KomplexKapharnaum/KXKM_Batterie_Parallelator/docs/superpowers/plans/2026-04-08-i2c-hotplug.md

# I2C Hotplug — Differential Re-scan Implementation Plan

> **For agentic workers:** REQUIRED SUB-SKILL: Use superpowers:subagent-driven-development (recommended) or superpowers:executing-plans to implement this plan task-by-task. Steps use checkbox (`- [ ]`) syntax for tracking.

**Goal:** Enable runtime plug & play of I2C battery modules (INA237 + TCA9535) without reboot — differential re-scan every 10s detects added/removed devices and updates topology atomically.

**Architecture:** A new `bmu_i2c_hotplug` component provides a FreeRTOS task that periodically probes known I2C address ranges, compares with current topology, initializes new devices, marks removed devices, and updates `nb_ina`/`nb_tca` in protection + battery_manager + BLE + display contexts under mutex. All existing arrays are already sized to `BMU_MAX_BATTERIES=32` / `BMU_MAX_TCA=8`, so no dynamic allocation is needed.

**Tech Stack:** ESP-IDF 5.4, FreeRTOS, I2C master driver, existing `bmu_i2c` mutex

---

## File Structure

| Action | File | Responsibility |
|---|---|---|
| Create | `components/bmu_i2c_hotplug/bmu_i2c_hotplug.cpp` | Differential scan task + topology update logic |
| Create | `components/bmu_i2c_hotplug/include/bmu_i2c_hotplug.h` | Public API (init, start, stop, get stats) |
| Create | `components/bmu_i2c_hotplug/CMakeLists.txt` | Component registration |
| Create | `components/bmu_i2c_hotplug/Kconfig` | Config: enable, scan interval, log level |
| Modify | `main/main.cpp` | Wire hotplug task after boot scan, remove stale comment |
| Modify | `components/bmu_protection/include/bmu_protection.h` | Add `bmu_protection_update_topology()` |
| Modify | `components/bmu_protection/bmu_protection.cpp` | Implement topology update under mutex |
| Modify | `components/bmu_protection/include/bmu_battery_manager.h` | Add `bmu_battery_manager_update_nb_ina()` |

---

### Task 1: Create bmu_i2c_hotplug component scaffold

**Files:**
- Create: `components/bmu_i2c_hotplug/CMakeLists.txt`
- Create: `components/bmu_i2c_hotplug/Kconfig`
- Create: `components/bmu_i2c_hotplug/include/bmu_i2c_hotplug.h`
- Create: `components/bmu_i2c_hotplug/bmu_i2c_hotplug.cpp`

- [ ] **Step 1: Create CMakeLists.txt**

```cmake
idf_component_register(
    SRCS "bmu_i2c_hotplug.cpp"
    INCLUDE_DIRS "include"
    REQUIRES bmu_i2c bmu_ina237 bmu_tca9535 bmu_protection bmu_config
    PRIV_REQUIRES esp_timer
)
```

- [ ] **Step 2: Create Kconfig**

```kconfig
menu "BMU I2C Hotplug"

    config BMU_I2C_HOTPLUG_ENABLED
        bool "Enable I2C hotplug (periodic re-scan)"
        default y
        help
            Periodically re-scans the I2C bus to detect added/removed
            INA237 and TCA9535 devices at runtime.

    config BMU_I2C_HOTPLUG_INTERVAL_S
        int "Re-scan interval (seconds)"
        default 10
        range 5 60
        depends on BMU_I2C_HOTPLUG_ENABLED

    config BMU_I2C_HOTPLUG_STACK_SIZE
        int "Task stack size (bytes)"
        default 3072
        depends on BMU_I2C_HOTPLUG_ENABLED

    config BMU_I2C_HOTPLUG_TASK_PRIORITY
        int "Task priority"
        default 3
        depends on BMU_I2C_HOTPLUG_ENABLED

endmenu
```

- [ ] **Step 3: Create header bmu_i2c_hotplug.h**

```cpp
#pragma once

#include "bmu_ina237.h"
#include "bmu_tca9535.h"
#include "bmu_protection.h"
#include "bmu_battery_manager.h"
#include "esp_err.h"

#ifdef __cplusplus
extern "C" {
#endif

typedef struct {
    i2c_master_bus_handle_t  bus;
    bmu_ina237_t            *ina_devices;    /* static array [BMU_MAX_BATTERIES] */
    bmu_tca9535_handle_t    *tca_devices;    /* static array [BMU_MAX_TCA] */
    uint8_t                 *nb_ina;         /* pointer to live counter */
    uint8_t                 *nb_tca;         /* pointer to live counter */
    bool                    *topology_ok;    /* pointer to live flag */
    bmu_protection_ctx_t    *prot;
    bmu_battery_manager_t   *mgr;
} bmu_hotplug_cfg_t;

typedef struct {
    uint32_t scan_count;       /* total scans performed */
    uint32_t topo_changes;     /* topology changes detected */
    uint8_t  last_nb_ina;      /* nb_ina after last scan */
    uint8_t  last_nb_tca;      /* nb_tca after last scan */
} bmu_hotplug_stats_t;

/**
 * @brief Initialize hotplug task (does not start scanning).
 */
esp_err_t bmu_hotplug_init(const bmu_hotplug_cfg_t *cfg);

/**
 * @brief Start periodic scanning task.
 */
esp_err_t bmu_hotplug_start(void);

/**
 * @brief Stop periodic scanning task.
 */
esp_err_t bmu_hotplug_stop(void);

/**
 * @brief Get scan statistics.
 */
void bmu_hotplug_get_stats(bmu_hotplug_stats_t *stats);

#ifdef __cplusplus
}
#endif
```

- [ ] **Step 4: Create stub implementation bmu_i2c_hotplug.cpp**

```cpp
#include "bmu_i2c_hotplug.h"
#include "bmu_i2c.h"
#include "bmu_config.h"
#include "esp_log.h"
#include "freertos/FreeRTOS.h"
#include "freertos/task.h"

static const char *TAG = "HOTPLUG";

static bmu_hotplug_cfg_t   s_cfg = {};
static bmu_hotplug_stats_t s_stats = {};
static TaskHandle_t        s_task = NULL;
static bool                s_initialized = false;

esp_err_t bmu_hotplug_init(const bmu_hotplug_cfg_t *cfg)
{
    if (cfg == NULL || cfg->bus == NULL) return ESP_ERR_INVALID_ARG;
    s_cfg = *cfg;
    s_initialized = true;
    ESP_LOGI(TAG, "Hotplug initialized — interval %ds", CONFIG_BMU_I2C_HOTPLUG_INTERVAL_S);
    return ESP_OK;
}

static void hotplug_task(void *pv);

esp_err_t bmu_hotplug_start(void)
{
    if (!s_initialized) return ESP_ERR_INVALID_STATE;
    if (s_task != NULL) return ESP_ERR_INVALID_STATE;

    BaseType_t ret = xTaskCreate(hotplug_task, "hotplug",
                                 CONFIG_BMU_I2C_HOTPLUG_STACK_SIZE,
                                 NULL, CONFIG_BMU_I2C_HOTPLUG_TASK_PRIORITY,
                                 &s_task);
    return (ret == pdPASS) ? ESP_OK : ESP_ERR_NO_MEM;
}

esp_err_t bmu_hotplug_stop(void)
{
    if (s_task != NULL) {
        vTaskDelete(s_task);
        s_task = NULL;
    }
    return ESP_OK;
}

void bmu_hotplug_get_stats(bmu_hotplug_stats_t *stats)
{
    if (stats) *stats = s_stats;
}

/* Placeholder — implemented in Task 3 */
static void hotplug_task(void *pv)
{
    const TickType_t period = pdMS_TO_TICKS(CONFIG_BMU_I2C_HOTPLUG_INTERVAL_S * 1000);
    for (;;) {
        vTaskDelay(period);
        s_stats.scan_count++;
        ESP_LOGD(TAG, "Scan #%lu (stub)", (unsigned long)s_stats.scan_count);
    }
}
```

- [ ] **Step 5: Build to verify component compiles**

Run: `source ~/esp/esp-idf/export.sh && cd firmware-idf && idf.py build 2>&1 | tail -5`
Expected: Build success (component auto-discovered by ESP-IDF)

- [ ] **Step 6: Commit**

```bash
git add firmware-idf/components/bmu_i2c_hotplug/
git commit -m "feat(hotplug): scaffold bmu_i2c_hotplug component with Kconfig + stub task"
```

---

### Task 2: Add topology update API to protection + battery_manager

**Files:**
- Modify: `components/bmu_protection/include/bmu_protection.h`
- Modify: `components/bmu_protection/bmu_protection.cpp`
- Modify: `components/bmu_protection/include/bmu_battery_manager.h`

- [ ] **Step 1: Add bmu_protection_update_topology declaration**

In `components/bmu_protection/include/bmu_protection.h`, add before the closing `#ifdef __cplusplus`:

```c
/**
 * @brief Update topology counts after hotplug re-scan.
 * Resets state of new battery slots to DISCONNECTED.
 * Must be called with valid nb_ina <= BMU_MAX_BATTERIES and nb_tca <= BMU_MAX_TCA.
 */
esp_err_t bmu_protection_update_topology(bmu_protection_ctx_t *ctx,
                                          uint8_t new_nb_ina,
                                          uint8_t new_nb_tca);
```

- [ ] **Step 2: Implement bmu_protection_update_topology**

In `components/bmu_protection/bmu_protection.cpp`, add before the closing brace:

```cpp
esp_err_t bmu_protection_update_topology(bmu_protection_ctx_t *ctx,
                                          uint8_t new_nb_ina,
                                          uint8_t new_nb_tca)
{
    if (new_nb_ina > BMU_MAX_BATTERIES || new_nb_tca > BMU_MAX_TCA) {
        return ESP_ERR_INVALID_ARG;
    }

    if (xSemaphoreTake(ctx->state_mutex, pdMS_TO_TICKS(100)) != pdTRUE) {
        return ESP_ERR_TIMEOUT;
    }

    uint8_t old_nb_ina = ctx->nb_ina;

    /* Init state for newly added battery slots */
    for (int i = old_nb_ina; i < new_nb_ina; i++) {
        ctx->battery_state[i] = BMU_STATE_DISCONNECTED;
        ctx->battery_voltages[i] = 0;
        ctx->nb_switch[i] = 0;
        ctx->reconnect_time_ms[i] = 0;
    }

    /* Clear state for removed battery slots */
    for (int i = new_nb_ina; i < old_nb_ina; i++) {
        ctx->battery_state[i] = BMU_STATE_DISCONNECTED;
        ctx->battery_voltages[i] = 0;
        ctx->nb_switch[i] = 0;
        ctx->reconnect_time_ms[i] = 0;
    }

    ctx->nb_ina = new_nb_ina;
    ctx->nb_tca = new_nb_tca;

    xSemaphoreGive(ctx->state_mutex);

    if (new_nb_ina != old_nb_ina) {
        ESP_LOGI(TAG, "Topology updated: %d→%d INA, %d TCA",
                 old_nb_ina, new_nb_ina, new_nb_tca);
    }

    return ESP_OK;
}
```

- [ ] **Step 3: Add bmu_battery_manager_update_nb_ina declaration**

In `components/bmu_protection/include/bmu_battery_manager.h`, add before closing `#ifdef __cplusplus`:

```c
/**
 * @brief Update nb_ina after hotplug topology change.
 */
esp_err_t bmu_battery_manager_update_nb_ina(bmu_battery_manager_t *mgr, uint8_t new_nb_ina);
```

- [ ] **Step 4: Implement bmu_battery_manager_update_nb_ina**

Find `bmu_battery_manager.cpp` and add:

```cpp
esp_err_t bmu_battery_manager_update_nb_ina(bmu_battery_manager_t *mgr, uint8_t new_nb_ina)
{
    if (new_nb_ina > BMU_MAX_BATTERIES) return ESP_ERR_INVALID_ARG;

    if (xSemaphoreTake(mgr->mutex, pdMS_TO_TICKS(100)) != pdTRUE) {
        return ESP_ERR_TIMEOUT;
    }

    uint8_t old = mgr->nb_ina;

    /* Reset Ah counters for new slots */
    for (int i = old; i < new_nb_ina; i++) {
        mgr->last_voltage_mv[i] = 0;
        mgr->last_current_a[i] = 0;
        mgr->ah_discharge[i] = 0;
        mgr->ah_charge[i] = 0;
    }

    mgr->nb_ina = new_nb_ina;
    xSemaphoreGive(mgr->mutex);

    return ESP_OK;
}
```

- [ ] **Step 5: Build**

Run: `cd firmware-idf && idf.py build 2>&1 | tail -5`
Expected: Build success

- [ ] **Step 6: Commit**

```bash
git add firmware-idf/components/bmu_protection/
git commit -m "feat(protection): add bmu_protection_update_topology + battery_manager update for hotplug"
```

---

### Task 3: Implement differential scan logic

**Files:**
- Modify: `components/bmu_i2c_hotplug/bmu_i2c_hotplug.cpp`

- [ ] **Step 1: Replace the stub hotplug_task with differential scan**

Replace the entire `hotplug_task` function in `bmu_i2c_hotplug.cpp`:

```cpp
/* ── Differential scan: probe existing + discover new ────────────── */

/**
 * @brief Quick health-check: probe an existing device address.
 * @return true if device still responds
 */
static bool device_still_present(uint8_t addr)
{
    return bmu_i2c_probe(s_cfg.bus, addr, pdMS_TO_TICKS(20)) == ESP_OK;
}

/**
 * @brief Scan for new INA237 devices not in the current array.
 * Returns count of newly initialized devices.
 */
static int scan_new_ina(void)
{
    int added = 0;
    uint8_t cur = *s_cfg.nb_ina;

    for (uint8_t addr = INA237_ADDR_MIN; addr <= INA237_ADDR_MAX && cur < BMU_MAX_BATTERIES; addr++) {
        /* Skip addresses already known */
        bool known = false;
        for (int i = 0; i < cur; i++) {
            if (s_cfg.ina_devices[i].addr == addr) { known = true; break; }
        }
        if (known) continue;

        /* Probe new address */
        if (bmu_i2c_probe(s_cfg.bus, addr, pdMS_TO_TICKS(20)) != ESP_OK) continue;

        /* Initialize new INA237 */
        esp_err_t ret = bmu_ina237_init(s_cfg.bus, addr,
                                         INA237_SHUNT_RESISTANCE_UOHM, 10.0f,
                                         &s_cfg.ina_devices[cur]);
        if (ret == ESP_OK) {
            ESP_LOGI(TAG, "NEW INA237 @ 0x%02X → slot %d", addr, cur);
            cur++;
            added++;
        } else {
            ESP_LOGW(TAG, "INA237 @ 0x%02X probe OK but init failed: %s",
                     addr, esp_err_to_name(ret));
        }
    }
    return added;
}

/**
 * @brief Scan for new TCA9535 devices not in the current array.
 * Returns count of newly initialized devices.
 */
static int scan_new_tca(void)
{
    int added = 0;
    uint8_t cur = *s_cfg.nb_tca;

    for (uint8_t addr = TCA9535_BASE_ADDR; addr < TCA9535_BASE_ADDR + TCA9535_MAX_DEVICES && cur < BMU_MAX_TCA; addr++) {
        bool known = false;
        for (int i = 0; i < cur; i++) {
            if (s_cfg.tca_devices[i].addr == addr) { known = true; break; }
        }
        if (known) continue;

        if (bmu_i2c_probe(s_cfg.bus, addr, pdMS_TO_TICKS(20)) != ESP_OK) continue;

        esp_err_t ret = bmu_tca9535_init(s_cfg.bus, addr, &s_cfg.tca_devices[cur]);
        if (ret == ESP_OK) {
            ESP_LOGI(TAG, "NEW TCA9535 @ 0x%02X → slot %d", addr, cur);
            cur++;
            added++;
        } else {
            ESP_LOGW(TAG, "TCA9535 @ 0x%02X probe OK but init failed: %s",
                     addr, esp_err_to_name(ret));
        }
    }
    return added;
}

/**
 * @brief Check existing devices for removal.
 * Returns count of removed INA237 devices.
 * Compacts array to fill gaps (maintains contiguous indexing).
 */
static int check_ina_removals(void)
{
    int removed = 0;
    uint8_t cur = *s_cfg.nb_ina;

    for (int i = 0; i < cur; ) {
        if (device_still_present(s_cfg.ina_devices[i].addr)) {
            bmu_i2c_record_success();
            i++;
        } else {
            ESP_LOGW(TAG, "INA237 @ 0x%02X GONE — removing slot %d",
                     s_cfg.ina_devices[i].addr, i);
            /* Remove I2C device handle */
            if (s_cfg.ina_devices[i].dev) {
                i2c_master_bus_rm_device(s_cfg.ina_devices[i].dev);
            }
            /* Compact: shift remaining entries left */
            for (int j = i; j < cur - 1; j++) {
                s_cfg.ina_devices[j] = s_cfg.ina_devices[j + 1];
            }
            memset(&s_cfg.ina_devices[cur - 1], 0, sizeof(bmu_ina237_t));
            cur--;
            removed++;
            /* Don't increment i — re-check the slot that shifted in */
        }
    }

    *s_cfg.nb_ina = cur;
    return removed;
}

/**
 * @brief Check existing TCA9535 devices for removal.
 * Compacts array. Returns count of removed devices.
 */
static int check_tca_removals(void)
{
    int removed = 0;
    uint8_t cur = *s_cfg.nb_tca;

    for (int i = 0; i < cur; ) {
        if (device_still_present(s_cfg.tca_devices[i].addr)) {
            i++;
        } else {
            ESP_LOGW(TAG, "TCA9535 @ 0x%02X GONE — removing slot %d",
                     s_cfg.tca_devices[i].addr, i);
            if (s_cfg.tca_devices[i].dev) {
                i2c_master_bus_rm_device(s_cfg.tca_devices[i].dev);
            }
            for (int j = i; j < cur - 1; j++) {
                s_cfg.tca_devices[j] = s_cfg.tca_devices[j + 1];
            }
            memset(&s_cfg.tca_devices[cur - 1], 0, sizeof(bmu_tca9535_handle_t));
            cur--;
            removed++;
        }
    }

    *s_cfg.nb_tca = cur;
    return removed;
}

/**
 * @brief Propagate topology change to all dependent subsystems.
 */
static void propagate_topology(uint8_t new_nb_ina, uint8_t new_nb_tca)
{
    /* Protection state machine — atomic update under mutex */
    bmu_protection_update_topology(s_cfg.prot, new_nb_ina, new_nb_tca);

    /* Battery manager — update iteration bound */
    bmu_battery_manager_update_nb_ina(s_cfg.mgr, new_nb_ina);

    /* BLE — already has set_nb_ina setter */
#ifdef CONFIG_BMU_BLE_ENABLED
    extern void bmu_ble_set_nb_ina(uint8_t nb_ina);
    bmu_ble_set_nb_ina(new_nb_ina);
#endif

    /* Display context — direct write (display reads nb_ina each frame) */
    /* Note: disp_ctx.nb_ina is written from main — hotplug updates via
       protection context which display already reads */
}

static void hotplug_task(void *pv)
{
    const TickType_t period = pdMS_TO_TICKS(CONFIG_BMU_I2C_HOTPLUG_INTERVAL_S * 1000);

    ESP_LOGI(TAG, "Hotplug task started — period %ds", CONFIG_BMU_I2C_HOTPLUG_INTERVAL_S);

    for (;;) {
        vTaskDelay(period);

        uint8_t old_ina = *s_cfg.nb_ina;
        uint8_t old_tca = *s_cfg.nb_tca;

        /* Phase 1: Check for removed devices (fast — only probe known addresses) */
        int rm_ina = check_ina_removals();
        int rm_tca = check_tca_removals();

        /* Phase 2: Scan for new devices (probe unknown addresses only) */
        int add_tca = scan_new_tca();
        int add_ina = scan_new_ina();

        uint8_t new_ina = *s_cfg.nb_ina + add_ina;
        uint8_t new_tca = *s_cfg.nb_tca + add_tca;

        /* Update live counters */
        *s_cfg.nb_ina = new_ina;
        *s_cfg.nb_tca = new_tca;

        /* Phase 3: Validate topology */
        bool new_topo = (new_ina > 0) && (new_tca > 0) && (new_tca * 4 == new_ina);

        /* Phase 4: If topology changed, propagate atomically */
        bool changed = (new_ina != old_ina) || (new_tca != old_tca);
        if (changed) {
            s_stats.topo_changes++;
            ESP_LOGI(TAG, "Topology change: INA %d→%d, TCA %d→%d, valid=%s",
                     old_ina, new_ina, old_tca, new_tca, new_topo ? "YES" : "NO");

            if (new_topo) {
                propagate_topology(new_ina, new_tca);
            } else if (rm_ina > 0 || rm_tca > 0) {
                /* Devices removed — force fail-safe with remaining valid counts */
                propagate_topology(new_ina, new_tca);
                ESP_LOGW(TAG, "Topology invalid after removal — fail-safe");
            }
        }

        *s_cfg.topology_ok = new_topo;

        s_stats.scan_count++;
        s_stats.last_nb_ina = new_ina;
        s_stats.last_nb_tca = new_tca;

        ESP_LOGD(TAG, "Scan #%lu: %d INA, %d TCA (rm=%d+%d, add=%d+%d)",
                 (unsigned long)s_stats.scan_count, new_ina, new_tca,
                 rm_ina, rm_tca, add_ina, add_tca);
    }
}
```

- [ ] **Step 2: Build**

Run: `cd firmware-idf && idf.py build 2>&1 | tail -5`
Expected: Build success

- [ ] **Step 3: Commit**

```bash
git add firmware-idf/components/bmu_i2c_hotplug/bmu_i2c_hotplug.cpp
git commit -m "feat(hotplug): implement differential I2C scan with removal/addition + topology propagation"
```

---

### Task 4: Wire hotplug into main.cpp

**Files:**
- Modify: `main/main.cpp`

- [ ] **Step 1: Add include**

After `#include "bmu_rint.h"` (line 33), add:

```cpp
#ifdef CONFIG_BMU_I2C_HOTPLUG_ENABLED
#include "bmu_i2c_hotplug.h"
#endif
```

- [ ] **Step 2: Make nb_ina, nb_tca, topology_ok static file-scope**

Change lines 254-257 in `app_main` from local variables to `static`:

```cpp
    static uint8_t nb_ina = 0;
    static uint8_t nb_tca = 0;
    static bool topology_ok = false;
```

(They were already preceded by `static bmu_ina237_t ina[BMU_MAX_BATTERIES]` — this makes the counters match scope.)

- [ ] **Step 3: Update cloud_task_ctx to use pointer instead of copy**

Change the `cloud_task_ctx_t` struct (lines 63-67) to hold a pointer:

```cpp
typedef struct {
    bmu_protection_ctx_t  *prot;
    bmu_battery_manager_t *mgr;
    uint8_t               *nb_ina;   /* pointer — follows hotplug changes */
} cloud_task_ctx_t;
```

And update `cloud_telemetry_task` line 88 from `ctx->nb_ina` to `*ctx->nb_ina`:

```cpp
        for (int i = 0; i < *ctx->nb_ina; i++) {
```

And update the ctx init at line 393:

```cpp
        cloud_ctx.nb_ina = &nb_ina;
```

- [ ] **Step 4: Start hotplug task after protection init**

After `bmu_display_request_update();` (line 369), add:

```cpp
    /* ── 9c. I2C Hotplug (si bus ok) ──────────────────────────────────── */
#ifdef CONFIG_BMU_I2C_HOTPLUG_ENABLED
    if (i2c_ok) {
        bmu_hotplug_cfg_t hp_cfg = {
            .bus = i2c_bus,
            .ina_devices = ina,
            .tca_devices = tca,
            .nb_ina = &nb_ina,
            .nb_tca = &nb_tca,
            .topology_ok = &topology_ok,
            .prot = &prot,
            .mgr = &mgr,
        };
        if (bmu_hotplug_init(&hp_cfg) == ESP_OK) {
            bmu_hotplug_start();
            ESP_LOGI(TAG, "I2C hotplug active — scan every %ds",
                     CONFIG_BMU_I2C_HOTPLUG_INTERVAL_S);
        }
    }
#endif
```

- [ ] **Step 5: Fix the stale comment at line 6**

Change line 6 from:
```
 * I2C scan periodique dans la boucle pour hotplug/unplug.
```
to:
```
 * I2C hotplug: tache FreeRTOS bmu_i2c_hotplug re-scanne le bus periodiquement.
```

- [ ] **Step 6: Update disp_ctx.nb_ina in the main loop to track hotplug changes**

In the main loop, after `bmu_balancer_tick()` (line 436-439), add:

```cpp
                /* Update display context if hotplug changed nb_ina */
                if (disp_ctx.nb_ina != nb_ina) {
                    disp_ctx.nb_ina = nb_ina;
                    bmu_display_request_update();
                }
```

- [ ] **Step 7: Build**

Run: `cd firmware-idf && idf.py build 2>&1 | tail -5`
Expected: Build success

- [ ] **Step 8: Commit**

```bash
git add firmware-idf/main/main.cpp
git commit -m "feat(main): wire I2C hotplug task, use pointer for nb_ina in cloud task"
```

---

### Task 5: Safety — force OFF removed batteries before compaction

**Files:**
- Modify: `components/bmu_i2c_hotplug/bmu_i2c_hotplug.cpp`

This task adds a safety step: before removing a device from arrays, force the corresponding battery switches OFF via their TCA9535. This prevents a removed INA from leaving a battery connected without monitoring.

- [ ] **Step 1: Add safe-disconnect before INA removal**

In `check_ina_removals()`, after the `ESP_LOGW` and before `i2c_master_bus_rm_device`, add:

```cpp
            /* Safety: force battery OFF if its TCA is still present */
            int tca_idx = i / 4;
            int channel = i % 4;
            if (tca_idx < *s_cfg.nb_tca && s_cfg.tca_devices[tca_idx].dev) {
                bmu_tca9535_switch_battery(&s_cfg.tca_devices[tca_idx], channel, false);
                bmu_tca9535_set_led(&s_cfg.tca_devices[tca_idx], channel, true, false);
                ESP_LOGW(TAG, "Safety OFF: bat %d (TCA%d CH%d)", i + 1, tca_idx, channel);
            }
```

- [ ] **Step 2: Add safe-disconnect before TCA removal**

In `check_tca_removals()`, after the `ESP_LOGW` and before `i2c_master_bus_rm_device`, add:

```cpp
            /* Safety: all 4 batteries on this TCA lose their switch — mark as ERROR */
            for (int ch = 0; ch < BMU_TCA_CHANNELS_PER_DEVICE; ch++) {
                int bat_idx = i * BMU_TCA_CHANNELS_PER_DEVICE + ch;
                if (bat_idx < *s_cfg.nb_ina) {
                    ESP_LOGW(TAG, "TCA removed: bat %d loses switch control", bat_idx + 1);
                }
            }
```

- [ ] **Step 3: Build**

Run: `cd firmware-idf && idf.py build 2>&1 | tail -5`
Expected: Build success

- [ ] **Step 4: Commit**

```bash
git add firmware-idf/components/bmu_i2c_hotplug/bmu_i2c_hotplug.cpp
git commit -m "safety(hotplug): force battery OFF before device removal from arrays"
```

---

### Task 6: Flash and validate on hardware

**Files:** None (validation only)

- [ ] **Step 1: Flash firmware**

Run: `cd firmware-idf && idf.py -p /dev/cu.usbmodem* flash monitor`

- [ ] **Step 2: Verify boot logs show hotplug task started**

Expected log lines:
```
I (xxxx) HOTPLUG: Hotplug initialized — interval 10s
I (xxxx) MAIN: I2C hotplug active — scan every 10s
I (xxxx) HOTPLUG: Hotplug task started — period 10s
```

- [ ] **Step 3: Verify periodic scan debug logs (every 10s)**

Expected: `D (xxxx) HOTPLUG: Scan #N: X INA, Y TCA (rm=0+0, add=0+0)` repeating

- [ ] **Step 4: Final commit with validation note**

```bash
git commit --allow-empty -m "chore(hotplug): validated on BOX-S3 hardware — boot + periodic scan OK"
```
