KomplexKapharnaum/KXKM_Batterie_Parallelator/docs/superpowers/plans/2026-04-02-dual-i2c-32bat.md

# Dual I2C 32 Batteries Implementation Plan

> **For agentic workers:** REQUIRED SUB-SKILL: Use superpowers:subagent-driven-development (recommended) or superpowers:executing-plans to implement this plan task-by-task. Steps use checkbox (`- [ ]`) syntax for tracking.

**Goal:** Scale from 16 to 32 batteries by adding a software bit-bang I2C bus on GPIO38/39, with the same INA237+TCA9535 address space. Move VE.Direct to GPIO21 RX-only.

**Architecture:** New `bmu_i2c_bitbang` component provides a software I2C driver. The INA237 and TCA9535 drivers get a bus abstraction layer so they can work on either hardware or bit-bang bus. `main.cpp` scans both buses and merges devices into a single 0-31 indexed array. `BMU_MAX_BATTERIES` goes from 16 to 32.

**Tech Stack:** ESP-IDF v5.4, C++, GPIO bit-bang, FreeRTOS mutex

**Spec:** `docs/superpowers/specs/2026-04-02-dual-i2c-32bat-design.md`

---

## File Structure

| File | Action | Responsibility |
|---|---|---|
| `firmware-idf/components/bmu_i2c_bitbang/include/bmu_i2c_bitbang.h` | Create | Bit-bang I2C driver API |
| `firmware-idf/components/bmu_i2c_bitbang/bmu_i2c_bitbang.c` | Create | GPIO bit-bang implementation |
| `firmware-idf/components/bmu_i2c_bitbang/Kconfig` | Create | Enable/disable, GPIO pins, freq |
| `firmware-idf/components/bmu_i2c_bitbang/CMakeLists.txt` | Create | Component registration |
| `firmware-idf/test/test_i2c_bitbang/main/test_i2c_bitbang.cpp` | Create | Host tests for timing+protocol logic |
| `firmware-idf/components/bmu_ina237/include/bmu_ina237.h` | Modify | Add bit-bang scan variant |
| `firmware-idf/components/bmu_ina237/bmu_ina237.cpp` | Modify | Add bit-bang read/write wrappers |
| `firmware-idf/components/bmu_tca9535/include/bmu_tca9535.h` | Modify | Add bit-bang scan variant |
| `firmware-idf/components/bmu_tca9535/bmu_tca9535.cpp` | Modify | Add bit-bang read/write wrappers |
| `firmware-idf/components/bmu_config/include/bmu_config.h` | Modify | BMU_MAX_BATTERIES 16→32 |
| `firmware-idf/components/bmu_vedirect/Kconfig` | Modify | Default GPIO21 RX, TX=-1 |
| `firmware-idf/sdkconfig.defaults` | Modify | VE.Direct GPIO21, bit-bang enable |
| `firmware-idf/main/main.cpp` | Modify | Dual bus scan+merge |
| `firmware-idf/main/CMakeLists.txt` | Modify | Add bmu_i2c_bitbang dep |
| `firmware-idf/components/bmu_display/bmu_ui_main.cpp` | Modify | Arrays 16→32 |
| `firmware-idf/components/bmu_display/bmu_ui_soh.cpp` | Modify | Arrays 16→32 |
| `firmware-idf/components/bmu_ble/bmu_ble_battery_svc.cpp` | Modify | 32 characteristics |

---

### Task 1: Bit-bang I2C driver — scaffold + Kconfig

**Files:**
- Create: `firmware-idf/components/bmu_i2c_bitbang/Kconfig`
- Create: `firmware-idf/components/bmu_i2c_bitbang/include/bmu_i2c_bitbang.h`
- Create: `firmware-idf/components/bmu_i2c_bitbang/CMakeLists.txt`

- [ ] **Step 1: Create Kconfig**

Create `firmware-idf/components/bmu_i2c_bitbang/Kconfig`:

```
menu "BMU I2C Bit-bang (Bus 2)"
    config BMU_I2C_BB_ENABLED
        bool "Enable bit-bang I2C bus 2"
        default n
    config BMU_I2C_BB_SDA_GPIO
        int "SDA GPIO"
        default 38
        depends on BMU_I2C_BB_ENABLED
    config BMU_I2C_BB_SCL_GPIO
        int "SCL GPIO"
        default 39
        depends on BMU_I2C_BB_ENABLED
    config BMU_I2C_BB_FREQ_HZ
        int "Frequency (Hz)"
        default 50000
        range 10000 400000
        depends on BMU_I2C_BB_ENABLED
endmenu
```

- [ ] **Step 2: Create header**

Create `firmware-idf/components/bmu_i2c_bitbang/include/bmu_i2c_bitbang.h`:

```c
#pragma once

#include "esp_err.h"
#include <stdint.h>
#include <stddef.h>
#include <stdbool.h>

#ifdef __cplusplus
extern "C" {
#endif

typedef struct bmu_i2c_bb_ctx *bmu_i2c_bb_handle_t;

typedef struct {
    int      sda_gpio;
    int      scl_gpio;
    uint32_t freq_hz;   /* target frequency (actual may be lower) */
} bmu_i2c_bb_config_t;

/**
 * @brief Init bit-bang I2C bus. Configures GPIOs as open-drain.
 */
esp_err_t bmu_i2c_bb_init(const bmu_i2c_bb_config_t *cfg,
                           bmu_i2c_bb_handle_t *out_handle);

/**
 * @brief Write then read (combined transaction).
 *        write_len=0 for read-only, read_len=0 for write-only.
 */
esp_err_t bmu_i2c_bb_write_read(bmu_i2c_bb_handle_t handle,
                                 uint8_t addr,
                                 const uint8_t *write_buf,
                                 size_t write_len,
                                 uint8_t *read_buf,
                                 size_t read_len);

/**
 * @brief Write-only convenience.
 */
esp_err_t bmu_i2c_bb_write(bmu_i2c_bb_handle_t handle,
                            uint8_t addr,
                            const uint8_t *buf,
                            size_t len);

/**
 * @brief Scan address range, returns true if device ACKs.
 */
bool bmu_i2c_bb_probe(bmu_i2c_bb_handle_t handle, uint8_t addr);

/**
 * @brief Read a 16-bit register (big-endian, INA237/TCA style).
 */
esp_err_t bmu_i2c_bb_read_reg16(bmu_i2c_bb_handle_t handle,
                                 uint8_t addr, uint8_t reg,
                                 uint16_t *value);

/**
 * @brief Write a 16-bit register (big-endian).
 */
esp_err_t bmu_i2c_bb_write_reg16(bmu_i2c_bb_handle_t handle,
                                  uint8_t addr, uint8_t reg,
                                  uint16_t value);

#ifdef __cplusplus
}
#endif
```

- [ ] **Step 3: Create CMakeLists.txt**

Create `firmware-idf/components/bmu_i2c_bitbang/CMakeLists.txt`:

```cmake
idf_component_register(
    SRCS "bmu_i2c_bitbang.c"
    INCLUDE_DIRS "include"
    REQUIRES driver esp_rom
)
```

- [ ] **Step 4: Commit**

```bash
git add firmware-idf/components/bmu_i2c_bitbang/
git commit -m "feat(i2c-bb): bit-bang driver scaffold"
```

---

### Task 2: Bit-bang I2C driver — implementation

**Files:**
- Create: `firmware-idf/components/bmu_i2c_bitbang/bmu_i2c_bitbang.c`

- [ ] **Step 1: Implement the driver**

Create `firmware-idf/components/bmu_i2c_bitbang/bmu_i2c_bitbang.c`:

```c
/**
 * @file bmu_i2c_bitbang.c
 * @brief Software I2C (bit-bang) driver for ESP32-S3.
 *
 * GPIO open-drain with internal+external pull-ups.
 * Timing via esp_rom_delay_us() for precision.
 * Thread-safe via FreeRTOS mutex.
 */
#include "sdkconfig.h"

#if CONFIG_BMU_I2C_BB_ENABLED

#include "bmu_i2c_bitbang.h"
#include "driver/gpio.h"
#include "esp_rom_sys.h"
#include "esp_log.h"
#include "freertos/FreeRTOS.h"
#include "freertos/semphr.h"
#include <stdlib.h>

static const char *TAG = "I2C_BB";

typedef struct bmu_i2c_bb_ctx {
    int              sda;
    int              scl;
    uint32_t         half_period_us; /* half clock period */
    SemaphoreHandle_t mutex;
} bmu_i2c_bb_ctx_t;

/* ── GPIO helpers ─────────────────────────────────────────────────── */

static inline void sda_high(bmu_i2c_bb_ctx_t *c) { gpio_set_level(c->sda, 1); }
static inline void sda_low(bmu_i2c_bb_ctx_t *c)  { gpio_set_level(c->sda, 0); }
static inline void scl_high(bmu_i2c_bb_ctx_t *c) { gpio_set_level(c->scl, 1); }
static inline void scl_low(bmu_i2c_bb_ctx_t *c)  { gpio_set_level(c->scl, 0); }
static inline int  sda_read(bmu_i2c_bb_ctx_t *c) { return gpio_get_level(c->sda); }

static inline void delay(bmu_i2c_bb_ctx_t *c)
{
    esp_rom_delay_us(c->half_period_us);
}

/* ── I2C primitives ───────────────────────────────────────────────── */

static void i2c_start(bmu_i2c_bb_ctx_t *c)
{
    sda_high(c); delay(c);
    scl_high(c); delay(c);
    sda_low(c);  delay(c);
    scl_low(c);  delay(c);
}

static void i2c_stop(bmu_i2c_bb_ctx_t *c)
{
    sda_low(c);  delay(c);
    scl_high(c); delay(c);
    sda_high(c); delay(c);
}

static bool i2c_write_byte(bmu_i2c_bb_ctx_t *c, uint8_t byte)
{
    for (int i = 7; i >= 0; i--) {
        if (byte & (1 << i)) sda_high(c); else sda_low(c);
        delay(c);
        scl_high(c); delay(c);
        scl_low(c);  delay(c);
    }
    /* Read ACK */
    sda_high(c); delay(c);
    scl_high(c); delay(c);
    bool ack = (sda_read(c) == 0);
    scl_low(c); delay(c);
    return ack;
}

static uint8_t i2c_read_byte(bmu_i2c_bb_ctx_t *c, bool send_ack)
{
    uint8_t byte = 0;
    sda_high(c); /* release SDA for slave */
    for (int i = 7; i >= 0; i--) {
        delay(c);
        scl_high(c); delay(c);
        if (sda_read(c)) byte |= (1 << i);
        scl_low(c);
    }
    /* Send ACK/NACK */
    if (send_ack) sda_low(c); else sda_high(c);
    delay(c);
    scl_high(c); delay(c);
    scl_low(c);  delay(c);
    sda_high(c);
    return byte;
}

/* ── Public API ───────────────────────────────────────────────────── */

esp_err_t bmu_i2c_bb_init(const bmu_i2c_bb_config_t *cfg,
                           bmu_i2c_bb_handle_t *out_handle)
{
    if (!cfg || !out_handle) return ESP_ERR_INVALID_ARG;

    bmu_i2c_bb_ctx_t *ctx = calloc(1, sizeof(bmu_i2c_bb_ctx_t));
    if (!ctx) return ESP_ERR_NO_MEM;

    ctx->sda = cfg->sda_gpio;
    ctx->scl = cfg->scl_gpio;
    ctx->half_period_us = 500000 / cfg->freq_hz; /* T/2 in us */
    if (ctx->half_period_us < 1) ctx->half_period_us = 1;

    ctx->mutex = xSemaphoreCreateMutex();

    /* Configure GPIOs as open-drain output + input */
    gpio_config_t io_conf = {
        .pin_bit_mask = (1ULL << ctx->sda) | (1ULL << ctx->scl),
        .mode = GPIO_MODE_INPUT_OUTPUT_OD,
        .pull_up_en = GPIO_PULLUP_ENABLE,
        .pull_down_en = GPIO_PULLDOWN_DISABLE,
        .intr_type = GPIO_INTR_DISABLE,
    };
    gpio_config(&io_conf);

    /* Idle state: both lines high */
    sda_high(ctx);
    scl_high(ctx);

    *out_handle = ctx;
    ESP_LOGI(TAG, "Bit-bang I2C on GPIO%d/%d @ %luHz (T/2=%luus)",
             ctx->sda, ctx->scl,
             (unsigned long)cfg->freq_hz,
             (unsigned long)ctx->half_period_us);
    return ESP_OK;
}

esp_err_t bmu_i2c_bb_write_read(bmu_i2c_bb_handle_t handle,
                                 uint8_t addr,
                                 const uint8_t *write_buf,
                                 size_t write_len,
                                 uint8_t *read_buf,
                                 size_t read_len)
{
    bmu_i2c_bb_ctx_t *c = (bmu_i2c_bb_ctx_t *)handle;
    if (!c) return ESP_ERR_INVALID_ARG;

    xSemaphoreTake(c->mutex, portMAX_DELAY);

    esp_err_t ret = ESP_OK;

    if (write_len > 0) {
        i2c_start(c);
        if (!i2c_write_byte(c, (addr << 1) | 0)) { /* write address */
            i2c_stop(c);
            xSemaphoreGive(c->mutex);
            return ESP_ERR_NOT_FOUND;
        }
        for (size_t i = 0; i < write_len; i++) {
            if (!i2c_write_byte(c, write_buf[i])) {
                ret = ESP_FAIL;
                break;
            }
        }
        if (ret != ESP_OK) {
            i2c_stop(c);
            xSemaphoreGive(c->mutex);
            return ret;
        }
    }

    if (read_len > 0) {
        i2c_start(c); /* repeated start */
        if (!i2c_write_byte(c, (addr << 1) | 1)) { /* read address */
            i2c_stop(c);
            xSemaphoreGive(c->mutex);
            return ESP_ERR_NOT_FOUND;
        }
        for (size_t i = 0; i < read_len; i++) {
            read_buf[i] = i2c_read_byte(c, i < read_len - 1);
        }
    }

    i2c_stop(c);
    xSemaphoreGive(c->mutex);
    return ESP_OK;
}

esp_err_t bmu_i2c_bb_write(bmu_i2c_bb_handle_t handle,
                            uint8_t addr,
                            const uint8_t *buf, size_t len)
{
    return bmu_i2c_bb_write_read(handle, addr, buf, len, NULL, 0);
}

bool bmu_i2c_bb_probe(bmu_i2c_bb_handle_t handle, uint8_t addr)
{
    bmu_i2c_bb_ctx_t *c = (bmu_i2c_bb_ctx_t *)handle;
    if (!c) return false;

    xSemaphoreTake(c->mutex, portMAX_DELAY);
    i2c_start(c);
    bool ack = i2c_write_byte(c, (addr << 1) | 0);
    i2c_stop(c);
    xSemaphoreGive(c->mutex);
    return ack;
}

esp_err_t bmu_i2c_bb_read_reg16(bmu_i2c_bb_handle_t handle,
                                 uint8_t addr, uint8_t reg,
                                 uint16_t *value)
{
    uint8_t buf[2];
    esp_err_t ret = bmu_i2c_bb_write_read(handle, addr,
                                           &reg, 1, buf, 2);
    if (ret == ESP_OK) {
        *value = ((uint16_t)buf[0] << 8) | buf[1];
    }
    return ret;
}

esp_err_t bmu_i2c_bb_write_reg16(bmu_i2c_bb_handle_t handle,
                                  uint8_t addr, uint8_t reg,
                                  uint16_t value)
{
    uint8_t buf[3] = { reg, (uint8_t)(value >> 8), (uint8_t)(value & 0xFF) };
    return bmu_i2c_bb_write(handle, addr, buf, 3);
}

#else /* !CONFIG_BMU_I2C_BB_ENABLED */

#include "bmu_i2c_bitbang.h"
esp_err_t bmu_i2c_bb_init(const bmu_i2c_bb_config_t *c, bmu_i2c_bb_handle_t *h)
{ (void)c; (void)h; return ESP_OK; }
esp_err_t bmu_i2c_bb_write_read(bmu_i2c_bb_handle_t h, uint8_t a,
    const uint8_t *w, size_t wl, uint8_t *r, size_t rl)
{ (void)h; (void)a; (void)w; (void)wl; (void)r; (void)rl; return ESP_ERR_NOT_SUPPORTED; }
esp_err_t bmu_i2c_bb_write(bmu_i2c_bb_handle_t h, uint8_t a, const uint8_t *b, size_t l)
{ (void)h; (void)a; (void)b; (void)l; return ESP_ERR_NOT_SUPPORTED; }
bool bmu_i2c_bb_probe(bmu_i2c_bb_handle_t h, uint8_t a) { (void)h; (void)a; return false; }
esp_err_t bmu_i2c_bb_read_reg16(bmu_i2c_bb_handle_t h, uint8_t a, uint8_t r, uint16_t *v)
{ (void)h; (void)a; (void)r; (void)v; return ESP_ERR_NOT_SUPPORTED; }
esp_err_t bmu_i2c_bb_write_reg16(bmu_i2c_bb_handle_t h, uint8_t a, uint8_t r, uint16_t v)
{ (void)h; (void)a; (void)r; (void)v; return ESP_ERR_NOT_SUPPORTED; }

#endif
```

- [ ] **Step 2: Commit**

```bash
git add firmware-idf/components/bmu_i2c_bitbang/bmu_i2c_bitbang.c
git commit -m "feat(i2c-bb): bit-bang I2C driver implementation"
```

---

### Task 3: INA237 + TCA9535 bit-bang support

**Files:**
- Modify: `firmware-idf/components/bmu_ina237/include/bmu_ina237.h`
- Modify: `firmware-idf/components/bmu_ina237/bmu_ina237.cpp`
- Modify: `firmware-idf/components/bmu_ina237/CMakeLists.txt`
- Modify: `firmware-idf/components/bmu_tca9535/include/bmu_tca9535.h`
- Modify: `firmware-idf/components/bmu_tca9535/bmu_tca9535.cpp`
- Modify: `firmware-idf/components/bmu_tca9535/CMakeLists.txt`

- [ ] **Step 1: Add bit-bang variants to INA237 header**

In `bmu_ina237.h`, add after the existing `bmu_ina237_t` typedef:

```c
/* ── Bit-bang bus support ─────────────────────────────────────────── */
#include "bmu_i2c_bitbang.h"

typedef struct {
    bmu_i2c_bb_handle_t bb;        /**< Bit-bang bus handle */
    uint8_t             addr;      /**< 7-bit address */
    float               current_lsb;
    bool                ready;
} bmu_ina237_bb_t;

esp_err_t bmu_ina237_bb_init(bmu_i2c_bb_handle_t bb, uint8_t addr,
                              uint32_t r_shunt_uohm, float max_current_a,
                              bmu_ina237_bb_t *ctx);

esp_err_t bmu_ina237_bb_read_bus_voltage(const bmu_ina237_bb_t *ctx,
                                          float *voltage_mv);
esp_err_t bmu_ina237_bb_read_current(const bmu_ina237_bb_t *ctx,
                                      float *current_a);
esp_err_t bmu_ina237_bb_read_voltage_current(const bmu_ina237_bb_t *ctx,
                                              float *voltage_mv,
                                              float *current_a);
esp_err_t bmu_ina237_bb_scan_init(bmu_i2c_bb_handle_t bb,
                                   uint32_t r_shunt_uohm,
                                   float max_current_a,
                                   bmu_ina237_bb_t devices[],
                                   uint8_t *count);
```

- [ ] **Step 2: Implement bit-bang INA237 functions**

In `bmu_ina237.cpp`, add the bit-bang variants. They mirror the hardware variants but use `bmu_i2c_bb_read_reg16`/`bmu_i2c_bb_write_reg16` instead of `i2c_master_transmit_receive`:

```cpp
#if CONFIG_BMU_I2C_BB_ENABLED

esp_err_t bmu_ina237_bb_init(bmu_i2c_bb_handle_t bb, uint8_t addr,
                              uint32_t r_shunt_uohm, float max_current_a,
                              bmu_ina237_bb_t *ctx)
{
    ctx->bb = bb;
    ctx->addr = addr;
    ctx->ready = false;

    /* Verify manufacturer ID */
    uint16_t mfr = 0;
    esp_err_t ret = bmu_i2c_bb_read_reg16(bb, addr, INA237_REG_MANUFACTURER_ID, &mfr);
    if (ret != ESP_OK || mfr != INA237_MANUFACTURER_ID) {
        ESP_LOGW(TAG, "[0x%02X] BB not INA237 (MFR=0x%04X)", addr, mfr);
        return ESP_ERR_NOT_FOUND;
    }

    /* Reset */
    bmu_i2c_bb_write_reg16(bb, addr, INA237_REG_CONFIG, INA237_CONFIG_RST);
    vTaskDelay(pdMS_TO_TICKS(2));

    /* Calibration (same formula as hardware version) */
    ctx->current_lsb = max_current_a / 32768.0f;
    float shunt_cal = 819.2e6f * ctx->current_lsb * (float)r_shunt_uohm / 1e6f;
    uint16_t cal_reg = (uint16_t)(shunt_cal + 0.5f);
    bmu_i2c_bb_write_reg16(bb, addr, INA237_REG_SHUNT_CAL, cal_reg);

    /* ADC config */
    bmu_i2c_bb_write_reg16(bb, addr, INA237_REG_ADC_CONFIG, INA237_ADC_CONFIG_BMU);

    ctx->ready = true;
    ESP_LOGI(TAG, "[0x%02X] BB INA237 init OK", addr);
    return ESP_OK;
}

esp_err_t bmu_ina237_bb_read_bus_voltage(const bmu_ina237_bb_t *ctx,
                                          float *voltage_mv)
{
    if (!ctx->ready) return ESP_ERR_INVALID_STATE;
    uint16_t raw;
    esp_err_t ret = bmu_i2c_bb_read_reg16(ctx->bb, ctx->addr,
                                           INA237_REG_VBUS, &raw);
    if (ret == ESP_OK) {
        *voltage_mv = (float)(int16_t)raw * (float)INA237_VBUS_LSB_UV / 1000.0f;
    }
    return ret;
}

esp_err_t bmu_ina237_bb_read_current(const bmu_ina237_bb_t *ctx,
                                      float *current_a)
{
    if (!ctx->ready) return ESP_ERR_INVALID_STATE;
    uint16_t raw;
    esp_err_t ret = bmu_i2c_bb_read_reg16(ctx->bb, ctx->addr,
                                           INA237_REG_CURRENT, &raw);
    if (ret == ESP_OK) {
        *current_a = (float)(int16_t)raw * ctx->current_lsb;
    }
    return ret;
}

esp_err_t bmu_ina237_bb_read_voltage_current(const bmu_ina237_bb_t *ctx,
                                              float *voltage_mv,
                                              float *current_a)
{
    esp_err_t ret = bmu_ina237_bb_read_bus_voltage(ctx, voltage_mv);
    if (ret != ESP_OK) return ret;
    return bmu_ina237_bb_read_current(ctx, current_a);
}

esp_err_t bmu_ina237_bb_scan_init(bmu_i2c_bb_handle_t bb,
                                   uint32_t r_shunt_uohm,
                                   float max_current_a,
                                   bmu_ina237_bb_t devices[],
                                   uint8_t *count)
{
    *count = 0;
    ESP_LOGI(TAG, "BB scan INA237 (0x%02X-0x%02X)...",
             INA237_ADDR_MIN, INA237_ADDR_MAX);
    for (uint8_t addr = INA237_ADDR_MIN; addr <= INA237_ADDR_MAX; addr++) {
        if (!bmu_i2c_bb_probe(bb, addr)) continue;
        if (*count >= INA237_MAX_DEVICES) break;
        esp_err_t ret = bmu_ina237_bb_init(bb, addr, r_shunt_uohm,
                                            max_current_a,
                                            &devices[*count]);
        if (ret == ESP_OK) (*count)++;
    }
    ESP_LOGI(TAG, "BB scan: %d INA237", *count);
    return (*count > 0) ? ESP_OK : ESP_ERR_NOT_FOUND;
}

#endif /* CONFIG_BMU_I2C_BB_ENABLED */
```

- [ ] **Step 3: Add bit-bang variants to TCA9535**

Same pattern in `bmu_tca9535.h` — add:

```c
#include "bmu_i2c_bitbang.h"

typedef struct {
    bmu_i2c_bb_handle_t bb;
    uint8_t             addr;
    uint8_t             out_p0;
    uint8_t             out_p1;
} bmu_tca9535_bb_handle_t;

esp_err_t bmu_tca9535_bb_scan_init(bmu_i2c_bb_handle_t bb,
                                    bmu_tca9535_bb_handle_t *handles,
                                    uint8_t max_devices,
                                    uint8_t *found);

esp_err_t bmu_tca9535_bb_switch_battery(bmu_tca9535_bb_handle_t *h,
                                         uint8_t channel, bool on);
esp_err_t bmu_tca9535_bb_set_led(bmu_tca9535_bb_handle_t *h,
                                  uint8_t channel,
                                  bool red, bool green);
esp_err_t bmu_tca9535_bb_all_off(bmu_tca9535_bb_handle_t *h);
```

Implement in `bmu_tca9535.cpp` using `bmu_i2c_bb_read_reg16`/`write_reg16` — same logic as hardware variants but via bit-bang.

- [ ] **Step 4: Update CMakeLists deps**

Add `bmu_i2c_bitbang` to REQUIRES in both `bmu_ina237/CMakeLists.txt` and `bmu_tca9535/CMakeLists.txt`.

- [ ] **Step 5: Commit**

```bash
git add firmware-idf/components/bmu_ina237/ firmware-idf/components/bmu_tca9535/
git commit -m "feat: INA237 + TCA9535 bit-bang bus support"
```

---

### Task 4: BMU_MAX_BATTERIES 16→32 + VE.Direct GPIO21

**Files:**
- Modify: `firmware-idf/components/bmu_config/include/bmu_config.h`
- Modify: `firmware-idf/components/bmu_vedirect/Kconfig`
- Modify: `firmware-idf/sdkconfig.defaults`

- [ ] **Step 1: Update BMU_MAX_BATTERIES**

In `bmu_config.h`, change:

```c
#define BMU_MAX_BATTERIES       32
```

- [ ] **Step 2: Update VE.Direct Kconfig defaults**

In `firmware-idf/components/bmu_vedirect/Kconfig`, change TX default to -1 and RX to 21:

```
    config BMU_VEDIRECT_TX_GPIO
        int "TX GPIO (BMU to charger, -1 to disable)"
        default -1
        depends on BMU_VEDIRECT_ENABLED
    config BMU_VEDIRECT_RX_GPIO
        int "RX GPIO (charger to BMU)"
        default 21
        depends on BMU_VEDIRECT_ENABLED
```

- [ ] **Step 3: Update sdkconfig.defaults**

Change VE.Direct and add bit-bang section:

```
# ── VE.Direct (SmartSolar 150/35) ────────────────────────────────────
CONFIG_BMU_VEDIRECT_ENABLED=y
CONFIG_BMU_VEDIRECT_UART_NUM=2
CONFIG_BMU_VEDIRECT_RX_GPIO=21
CONFIG_BMU_VEDIRECT_TX_GPIO=-1
CONFIG_BMU_VEDIRECT_BAUD=19200

# ── I2C Bit-bang bus 2 (batteries 17-32) ─────────────────────────────
CONFIG_BMU_I2C_BB_ENABLED=y
CONFIG_BMU_I2C_BB_SDA_GPIO=38
CONFIG_BMU_I2C_BB_SCL_GPIO=39
CONFIG_BMU_I2C_BB_FREQ_HZ=50000
```

- [ ] **Step 4: Commit**

```bash
git add firmware-idf/components/bmu_config/ firmware-idf/components/bmu_vedirect/ firmware-idf/sdkconfig.defaults
git commit -m "feat: MAX_BATTERIES 32 + VE.Direct GPIO21 RX"
```

---

### Task 5: main.cpp — dual bus scan + merge

**Files:**
- Modify: `firmware-idf/main/main.cpp`
- Modify: `firmware-idf/main/CMakeLists.txt`

- [ ] **Step 1: Add bmu_i2c_bitbang to main deps**

In `firmware-idf/main/CMakeLists.txt`, add `bmu_i2c_bitbang` to REQUIRES.

- [ ] **Step 2: Modify main.cpp for dual bus**

Add include:
```cpp
#include "bmu_i2c_bitbang.h"
```

After the bus 1 scan block, add bus 2:

```cpp
    /* ── 8b. Bus 2 bit-bang (batteries 17-32) ──────────────────── */
#if CONFIG_BMU_I2C_BB_ENABLED
    static bmu_ina237_bb_t ina_bb[INA237_MAX_DEVICES] = {};
    uint8_t nb_ina_bb = 0;
    static bmu_tca9535_bb_handle_t tca_bb[TCA9535_MAX_DEVICES] = {};
    uint8_t nb_tca_bb = 0;
    bmu_i2c_bb_handle_t bb_bus = NULL;

    {
        bmu_i2c_bb_config_t bb_cfg = {
            .sda_gpio = CONFIG_BMU_I2C_BB_SDA_GPIO,
            .scl_gpio = CONFIG_BMU_I2C_BB_SCL_GPIO,
            .freq_hz = CONFIG_BMU_I2C_BB_FREQ_HZ,
        };
        if (bmu_i2c_bb_init(&bb_cfg, &bb_bus) == ESP_OK) {
            ESP_LOGI(TAG, "I2C bus 2 (bit-bang) OK");
            bmu_ina237_bb_scan_init(bb_bus, 2000, 10.0f,
                                     ina_bb, &nb_ina_bb);
            ESP_LOGI(TAG, "Bus 2 INA237: %d", nb_ina_bb);
            bmu_tca9535_bb_scan_init(bb_bus, tca_bb,
                                     TCA9535_MAX_DEVICES,
                                     &nb_tca_bb);
            ESP_LOGI(TAG, "Bus 2 TCA9535: %d", nb_tca_bb);
        }
    }
#else
    uint8_t nb_ina_bb = 0;
    uint8_t nb_tca_bb = 0;
#endif

    /* ── Total batteries ── */
    uint8_t total_ina = nb_ina + nb_ina_bb;
    uint8_t total_tca = nb_tca + nb_tca_bb;
    ESP_LOGI(TAG, "Total: %d INA, %d TCA (%d + %d batteries)",
             total_ina, total_tca, nb_ina, nb_ina_bb);
```

Update topology check:
```cpp
    bool bus1_ok = (nb_ina == 0 && nb_tca == 0) ||
                   (nb_tca * 4 == nb_ina);
    bool bus2_ok = (nb_ina_bb == 0 && nb_tca_bb == 0) ||
                   (nb_tca_bb * 4 == nb_ina_bb);
    topology_ok = bus1_ok && bus2_ok;
```

Update `disp_ctx.nb_ina`:
```cpp
    disp_ctx.nb_ina = total_ina;
```

- [ ] **Step 3: Commit**

```bash
git add firmware-idf/main/
git commit -m "feat: dual I2C bus scan + merge in main"
```

---

### Task 6: UI arrays 16→32

**Files:**
- Modify: `firmware-idf/components/bmu_display/bmu_ui_main.cpp`
- Modify: `firmware-idf/components/bmu_display/bmu_ui_soh.cpp`

- [ ] **Step 1: Update static arrays to 32**

In `bmu_ui_main.cpp`, change all `[16]` to `[32]`:
```cpp
static lv_obj_t *s_bat_rows[32]    = {};
static lv_obj_t *s_bat_bars[32]    = {};
static lv_obj_t *s_bat_vlabels[32] = {};
static lv_obj_t *s_bat_ilabels[32] = {};
static lv_obj_t *s_bat_borders[32] = {};
```

In `ensure_battery_rows`, change `if (nb > 16) nb = 16;` to `if (nb > 32) nb = 32;`.

In `bmu_ui_soh.cpp`, change all `[16]` to `[32]`:
```cpp
static lv_obj_t *s_soh_bars[32]        = {};
static lv_obj_t *s_soh_pct_labels[32]  = {};
static lv_obj_t *s_soh_warn_labels[32] = {};
```

In `ensure_soh_rows`, change `if (nb > 16) nb = 16;` to `if (nb > 32) nb = 32;`.

- [ ] **Step 2: Commit**

```bash
git add firmware-idf/components/bmu_display/
git commit -m "feat(ui): extend arrays to 32 batteries"
```

---

### Task 7: BLE — 32 battery characteristics

**Files:**
- Modify: `firmware-idf/components/bmu_ble/bmu_ble_battery_svc.cpp`

- [ ] **Step 1: Extend BLE characteristics**

The existing battery service creates characteristics 0x0010-0x001F (16 batteries). Extend to 0x0010-0x002F (32 batteries).

Find the UUID declaration array and the characteristic registration loop. Change the loop upper bound from `BMU_MAX_BATTERIES` (was 16, now 32). The UUIDs auto-increment: `BMU_BLE_UUID128_DECLARE(0x10 + i, 0x00)`.

The notification timer already iterates on `bmu_ble_get_nb_ina()` which will return the actual count (up to 32).

- [ ] **Step 2: Commit**

```bash
git add firmware-idf/components/bmu_ble/
git commit -m "feat(ble): extend to 32 battery characteristics"
```

---

### Task 8: Host test — bit-bang protocol logic

**Files:**
- Create: `firmware-idf/test/test_i2c_bitbang/main/test_i2c_bitbang.cpp`

- [ ] **Step 1: Create test file**

Tests the protocol logic (address encoding, register read/write format, probe) without actual GPIO.

```cpp
#ifdef NATIVE_TEST

#include "unity.h"
#include <cstdint>

extern "C" void setUp(void) {}
extern "C" void tearDown(void) {}

/* Test I2C address byte formatting */
void test_write_address_byte(void)
{
    uint8_t addr = 0x40;
    uint8_t write_byte = (addr << 1) | 0;
    TEST_ASSERT_EQUAL_UINT8(0x80, write_byte);
}

void test_read_address_byte(void)
{
    uint8_t addr = 0x40;
    uint8_t read_byte = (addr << 1) | 1;
    TEST_ASSERT_EQUAL_UINT8(0x81, read_byte);
}

void test_reg16_big_endian_pack(void)
{
    uint16_t value = 0x1234;
    uint8_t buf[3];
    buf[0] = 0x05; /* register */
    buf[1] = (uint8_t)(value >> 8);
    buf[2] = (uint8_t)(value & 0xFF);
    TEST_ASSERT_EQUAL_UINT8(0x05, buf[0]);
    TEST_ASSERT_EQUAL_UINT8(0x12, buf[1]);
    TEST_ASSERT_EQUAL_UINT8(0x34, buf[2]);
}

void test_reg16_big_endian_unpack(void)
{
    uint8_t buf[2] = { 0xAB, 0xCD };
    uint16_t value = ((uint16_t)buf[0] << 8) | buf[1];
    TEST_ASSERT_EQUAL_UINT16(0xABCD, value);
}

void test_half_period_50khz(void)
{
    uint32_t freq = 50000;
    uint32_t half_period = 500000 / freq;
    TEST_ASSERT_EQUAL_UINT32(10, half_period); /* 10us */
}

void test_half_period_100khz(void)
{
    uint32_t freq = 100000;
    uint32_t half_period = 500000 / freq;
    TEST_ASSERT_EQUAL_UINT32(5, half_period);
}

void test_address_range_ina237(void)
{
    for (uint8_t a = 0x40; a <= 0x4F; a++) {
        uint8_t wb = (a << 1) | 0;
        TEST_ASSERT_TRUE(wb >= 0x80 && wb <= 0x9E);
    }
}

void test_address_range_tca9535(void)
{
    for (uint8_t a = 0x20; a <= 0x27; a++) {
        uint8_t wb = (a << 1) | 0;
        TEST_ASSERT_TRUE(wb >= 0x40 && wb <= 0x4E);
    }
}

int main(void)
{
    UNITY_BEGIN();
    RUN_TEST(test_write_address_byte);
    RUN_TEST(test_read_address_byte);
    RUN_TEST(test_reg16_big_endian_pack);
    RUN_TEST(test_reg16_big_endian_unpack);
    RUN_TEST(test_half_period_50khz);
    RUN_TEST(test_half_period_100khz);
    RUN_TEST(test_address_range_ina237);
    RUN_TEST(test_address_range_tca9535);
    return UNITY_END();
}

#endif
```

- [ ] **Step 2: Add to Makefile**

Add `test_i2c_bitbang` to the `TESTS` list in `firmware-idf/test/Makefile`.

- [ ] **Step 3: Run tests**

```bash
cd firmware-idf/test && make all
```

- [ ] **Step 4: Commit**

```bash
git add firmware-idf/test/
git commit -m "test(i2c-bb): host tests for protocol logic"
```

---

### Task 9: Integration build + flash

**Files:** None (verification only)

- [ ] **Step 1: Clean build**

```bash
cd firmware-idf && rm -rf build/sdkconfig
export IDF_PATH=$HOME/esp/esp-idf && . $IDF_PATH/export.sh
idf.py build 2>&1 | tail -10
```

Expected: `Project build complete`

- [ ] **Step 2: Run host tests**

```bash
cd firmware-idf/test && make clean && make all
```

Expected: 6 suites, all passing (88+ tests)

- [ ] **Step 3: Flash**

```bash
idf.py -p /dev/cu.usbmodem* flash
```

- [ ] **Step 4: Verify**

Serial monitor — check:
- Bus 1 scan: INA/TCA detected
- Bus 2 (bit-bang): init message, 0 devices (no hardware connected)
- VE.Direct on GPIO21
- No crash, no watchdog
- UI works with bus 1 batteries

- [ ] **Step 5: Commit**

```bash
git add -A
git commit -m "feat: dual I2C 32 batteries complete"
```
