KomplexKapharnaum/KXKM_Batterie_Parallelator/docs/superpowers/plans/2026-04-01-bmu-app-plan3-android.md

# BMU App — Plan 3: Android Jetpack Compose App

> **For agentic workers:** REQUIRED SUB-SKILL: Use superpowers:subagent-driven-development (recommended) or superpowers:executing-plans to implement this plan task-by-task. Steps use checkbox (`- [ ]`) syntax for tracking.

**Goal:** Build the Android native UI for the KXKM BMU companion app using Jetpack Compose + Material3, consuming the KMP shared module for all business logic, transport, auth, and data persistence.

**Architecture:** Thin Compose layer over the KMP shared module. ViewModels wrap shared use cases and expose `StateFlow` state. Navigation via bottom `NavigationBar` (5 tabs). The shared module handles BLE, WiFi, MQTT, REST, SQLDelight, auth — Android only does UI + platform permissions.

**Tech Stack:** Jetpack Compose, Material3, Navigation Compose, Vico (charts), Hilt (DI), AndroidX BiometricPrompt

**Depends on:** Plan 2 (KMP shared module must be built first)

**Spec:** `docs/superpowers/specs/2026-04-01-smartphone-app-design.md`

---

## File Structure

```
androidApp/
├── build.gradle.kts
├── src/main/
│   ├── AndroidManifest.xml
│   ├── java/com/kxkm/bmu/
│   │   ├── BmuApplication.kt                  # Hilt Application
│   │   ├── MainActivity.kt                    # Single Activity, setContent
│   │   ├── di/
│   │   │   └── AppModule.kt                   # Hilt providers for KMP use cases
│   │   ├── viewmodel/
│   │   │   ├── AuthViewModel.kt               # PIN entry, session, role
│   │   │   ├── DashboardViewModel.kt          # Battery grid state
│   │   │   ├── BatteryDetailViewModel.kt      # Single battery + history chart
│   │   │   ├── SystemViewModel.kt             # System info + solar
│   │   │   ├── AuditViewModel.kt              # Audit trail + filters
│   │   │   └── ConfigViewModel.kt             # Config + WiFi + users
│   │   ├── ui/
│   │   │   ├── BmuNavHost.kt                  # Navigation graph
│   │   │   ├── auth/
│   │   │   │   ├── PinEntryScreen.kt          # PIN pad (6 digits)
│   │   │   │   └── OnboardingScreen.kt        # First-launch admin setup
│   │   │   ├── dashboard/
│   │   │   │   ├── DashboardScreen.kt         # Battery grid
│   │   │   │   └── BatteryCellCard.kt         # Single battery card
│   │   │   ├── detail/
│   │   │   │   ├── BatteryDetailScreen.kt     # Full detail screen
│   │   │   │   └── VoltageChart.kt            # Vico chart history
│   │   │   ├── system/
│   │   │   │   └── SystemScreen.kt            # System + solar info
│   │   │   ├── audit/
│   │   │   │   ├── AuditScreen.kt             # Event list + filters
│   │   │   │   └── AuditEventRow.kt           # Single event row
│   │   │   ├── config/
│   │   │   │   ├── ConfigScreen.kt            # Settings root
│   │   │   │   ├── ProtectionConfigScreen.kt  # V/I thresholds
│   │   │   │   ├── WifiConfigScreen.kt        # BMU WiFi setup
│   │   │   │   ├── UserManagementScreen.kt    # User CRUD
│   │   │   │   ├── SyncConfigScreen.kt        # Cloud sync settings
│   │   │   │   └── TransportConfigScreen.kt   # Channel selection
│   │   │   ├── components/
│   │   │   │   ├── StatusBar.kt               # Transport indicator
│   │   │   │   ├── BatteryStateIcon.kt        # Color-coded state icon
│   │   │   │   └── ConfirmActionDialog.kt     # Switch ON/OFF confirm
│   │   │   └── theme/
│   │   │       ├── Theme.kt                   # Material3 dynamic color
│   │   │       ├── Color.kt                   # KXKM palette
│   │   │       └── Type.kt                    # Typography
│   │   └── util/
│   │       ├── SharedBridge.kt                # KMP type extensions
│   │       └── BiometricHelper.kt             # AndroidX BiometricPrompt
│   └── res/
│       ├── values/strings.xml
│       └── mipmap-*/ (launcher icons)
```

---

### Task 1: Android project setup + KMP shared module integration

**Files:**
- Create: `androidApp/build.gradle.kts`
- Create: `androidApp/src/main/AndroidManifest.xml`
- Create: `androidApp/src/main/java/com/kxkm/bmu/BmuApplication.kt`
- Create: `androidApp/src/main/java/com/kxkm/bmu/MainActivity.kt`

- [ ] **Step 1: Create Android module directory**

```bash
cd kxkm-bmu-app
mkdir -p androidApp/src/main/java/com/kxkm/bmu
mkdir -p androidApp/src/main/res/values
```

- [ ] **Step 2: Create build.gradle.kts**

Create `androidApp/build.gradle.kts`:

```kotlin
plugins {
    id("com.android.application")
    id("org.jetbrains.kotlin.android")
    id("com.google.dagger.hilt.android")
    id("com.google.devtools.ksp")
}

android {
    namespace = "com.kxkm.bmu"
    compileSdk = 35

    defaultConfig {
        applicationId = "com.kxkm.bmu"
        minSdk = 26
        targetSdk = 35
        versionCode = 1
        versionName = "1.0.0"
    }

    buildFeatures {
        compose = true
    }

    composeOptions {
        kotlinCompilerExtensionVersion = "1.5.14"
    }

    compileOptions {
        sourceCompatibility = JavaVersion.VERSION_17
        targetCompatibility = JavaVersion.VERSION_17
    }

    kotlinOptions {
        jvmTarget = "17"
    }
}

dependencies {
    implementation(project(":shared"))

    // Compose BOM
    val composeBom = platform("androidx.compose:compose-bom:2025.01.01")
    implementation(composeBom)
    implementation("androidx.compose.material3:material3")
    implementation("androidx.compose.ui:ui")
    implementation("androidx.compose.ui:ui-tooling-preview")
    debugImplementation("androidx.compose.ui:ui-tooling")

    // Navigation Compose
    implementation("androidx.navigation:navigation-compose:2.8.5")

    // Lifecycle + ViewModel
    implementation("androidx.lifecycle:lifecycle-viewmodel-compose:2.8.7")
    implementation("androidx.lifecycle:lifecycle-runtime-compose:2.8.7")

    // Hilt
    implementation("com.google.dagger:hilt-android:2.52")
    ksp("com.google.dagger:hilt-compiler:2.52")
    implementation("androidx.hilt:hilt-navigation-compose:1.2.0")

    // Vico charts
    implementation("com.patrykandpatrick.vico:compose-m3:2.0.1")

    // Biometric
    implementation("androidx.biometric:biometric:1.1.0")

    // Activity Compose
    implementation("androidx.activity:activity-compose:1.9.3")
}
```

- [ ] **Step 3: Add to root settings.gradle.kts**

Ensure `settings.gradle.kts` includes:

```kotlin
include(":androidApp")
include(":shared")
```

- [ ] **Step 4: Create AndroidManifest.xml**

Create `androidApp/src/main/AndroidManifest.xml`:

```xml
<?xml version="1.0" encoding="utf-8"?>
<manifest xmlns:android="http://schemas.android.com/apk/res/android">

    <!-- BLE permissions -->
    <uses-permission android:name="android.permission.BLUETOOTH" />
    <uses-permission android:name="android.permission.BLUETOOTH_ADMIN" />
    <uses-permission android:name="android.permission.BLUETOOTH_SCAN" />
    <uses-permission android:name="android.permission.BLUETOOTH_CONNECT" />
    <uses-permission android:name="android.permission.ACCESS_FINE_LOCATION" />

    <!-- WiFi / network -->
    <uses-permission android:name="android.permission.INTERNET" />
    <uses-permission android:name="android.permission.ACCESS_NETWORK_STATE" />
    <uses-permission android:name="android.permission.ACCESS_WIFI_STATE" />

    <!-- Biometric -->
    <uses-permission android:name="android.permission.USE_BIOMETRIC" />

    <uses-feature android:name="android.hardware.bluetooth_le" android:required="true" />

    <application
        android:name=".BmuApplication"
        android:label="KXKM BMU"
        android:icon="@mipmap/ic_launcher"
        android:theme="@style/Theme.Material3.DayNight.NoActionBar"
        android:supportsRtl="true">

        <activity
            android:name=".MainActivity"
            android:exported="true"
            android:windowSoftInputMode="adjustResize">
            <intent-filter>
                <action android:name="android.intent.action.MAIN" />
                <category android:name="android.intent.category.LAUNCHER" />
            </intent-filter>
        </activity>
    </application>
</manifest>
```

- [ ] **Step 5: Create BmuApplication**

Create `androidApp/src/main/java/com/kxkm/bmu/BmuApplication.kt`:

```kotlin
package com.kxkm.bmu

import android.app.Application
import dagger.hilt.android.HiltAndroidApp

@HiltAndroidApp
class BmuApplication : Application()
```

- [ ] **Step 6: Create MainActivity**

Create `androidApp/src/main/java/com/kxkm/bmu/MainActivity.kt`:

```kotlin
package com.kxkm.bmu

import android.os.Bundle
import androidx.activity.ComponentActivity
import androidx.activity.compose.setContent
import androidx.activity.enableEdgeToEdge
import androidx.compose.runtime.collectAsState
import androidx.compose.runtime.getValue
import androidx.hilt.navigation.compose.hiltViewModel
import com.kxkm.bmu.ui.BmuNavHost
import com.kxkm.bmu.ui.auth.OnboardingScreen
import com.kxkm.bmu.ui.auth.PinEntryScreen
import com.kxkm.bmu.ui.theme.BmuTheme
import com.kxkm.bmu.viewmodel.AuthViewModel
import dagger.hilt.android.AndroidEntryPoint

@AndroidEntryPoint
class MainActivity : ComponentActivity() {
    override fun onCreate(savedInstanceState: Bundle?) {
        super.onCreate(savedInstanceState)
        enableEdgeToEdge()
        setContent {
            BmuTheme {
                val authVM: AuthViewModel = hiltViewModel()
                val isAuthenticated by authVM.isAuthenticated.collectAsState()
                val needsOnboarding by authVM.needsOnboarding.collectAsState()

                when {
                    needsOnboarding -> OnboardingScreen(authVM = authVM)
                    !isAuthenticated -> PinEntryScreen(authVM = authVM)
                    else -> BmuNavHost(authVM = authVM)
                }
            }
        }
    }
}
```

- [ ] **Step 7: Create strings.xml**

Create `androidApp/src/main/res/values/strings.xml`:

```xml
<?xml version="1.0" encoding="utf-8"?>
<resources>
    <string name="app_name">KXKM BMU</string>
    <string name="tab_batteries">Batteries</string>
    <string name="tab_system">Système</string>
    <string name="tab_audit">Audit</string>
    <string name="tab_config">Config</string>
    <string name="ble_permission_rationale">KXKM BMU utilise le Bluetooth pour communiquer avec le boîtier de gestion batteries.</string>
    <string name="biometric_prompt_title">Déverrouiller KXKM BMU</string>
    <string name="biometric_prompt_subtitle">Utilisez votre empreinte ou votre visage</string>
</resources>
```

- [ ] **Step 8: Build to verify**

```bash
cd kxkm-bmu-app && ./gradlew :androidApp:assembleDebug 2>&1 | tail -5
```
Expected: `BUILD SUCCESSFUL`

- [ ] **Step 9: Commit**

```bash
git add androidApp/
git commit -m "feat(android): project setup with Compose, Hilt, KMP shared dependency"
```

---

### Task 2: Theme + KMP bridge helpers

**Files:**
- Create: `androidApp/src/main/java/com/kxkm/bmu/ui/theme/Color.kt`
- Create: `androidApp/src/main/java/com/kxkm/bmu/ui/theme/Type.kt`
- Create: `androidApp/src/main/java/com/kxkm/bmu/ui/theme/Theme.kt`
- Create: `androidApp/src/main/java/com/kxkm/bmu/util/SharedBridge.kt`

- [ ] **Step 1: Create Color.kt**

```kotlin
package com.kxkm.bmu.ui.theme

import androidx.compose.ui.graphics.Color

// KXKM brand palette
val KxkmGreen = Color(0xFF4CAF50)
val KxkmRed = Color(0xFFF44336)
val KxkmOrange = Color(0xFFFF9800)
val KxkmYellow = Color(0xFFFFEB3B)
val KxkmBlue = Color(0xFF2196F3)

// Battery state colors
val BatteryConnected = Color(0xFF4CAF50)
val BatteryDisconnected = Color(0xFFF44336)
val BatteryReconnecting = Color(0xFFFFEB3B)
val BatteryError = Color(0xFFFF9800)
val BatteryLocked = Color(0xFFF44336)
```

- [ ] **Step 2: Create Type.kt**

```kotlin
package com.kxkm.bmu.ui.theme

import androidx.compose.material3.Typography
import androidx.compose.ui.text.TextStyle
import androidx.compose.ui.text.font.FontFamily
import androidx.compose.ui.text.font.FontWeight
import androidx.compose.ui.unit.sp

val BmuTypography = Typography(
    headlineLarge = TextStyle(
        fontFamily = FontFamily.Default,
        fontWeight = FontWeight.Bold,
        fontSize = 28.sp,
        lineHeight = 36.sp,
    ),
    titleLarge = TextStyle(
        fontFamily = FontFamily.Default,
        fontWeight = FontWeight.Bold,
        fontSize = 22.sp,
        lineHeight = 28.sp,
    ),
    bodyLarge = TextStyle(
        fontFamily = FontFamily.Default,
        fontWeight = FontWeight.Normal,
        fontSize = 16.sp,
        lineHeight = 24.sp,
    ),
    labelSmall = TextStyle(
        fontFamily = FontFamily.Default,
        fontWeight = FontWeight.Medium,
        fontSize = 11.sp,
        lineHeight = 16.sp,
    ),
)
```

- [ ] **Step 3: Create Theme.kt**

```kotlin
package com.kxkm.bmu.ui.theme

import android.os.Build
import androidx.compose.foundation.isSystemInDarkTheme
import androidx.compose.material3.MaterialTheme
import androidx.compose.material3.darkColorScheme
import androidx.compose.material3.dynamicDarkColorScheme
import androidx.compose.material3.dynamicLightColorScheme
import androidx.compose.material3.lightColorScheme
import androidx.compose.runtime.Composable
import androidx.compose.ui.platform.LocalContext

private val DarkColorScheme = darkColorScheme(
    primary = KxkmGreen,
    secondary = KxkmBlue,
    error = KxkmRed,
)

private val LightColorScheme = lightColorScheme(
    primary = KxkmGreen,
    secondary = KxkmBlue,
    error = KxkmRed,
)

@Composable
fun BmuTheme(
    darkTheme: Boolean = isSystemInDarkTheme(),
    dynamicColor: Boolean = true,
    content: @Composable () -> Unit,
) {
    val colorScheme = when {
        dynamicColor && Build.VERSION.SDK_INT >= Build.VERSION_CODES.S -> {
            val context = LocalContext.current
            if (darkTheme) dynamicDarkColorScheme(context) else dynamicLightColorScheme(context)
        }
        darkTheme -> DarkColorScheme
        else -> LightColorScheme
    }

    MaterialTheme(
        colorScheme = colorScheme,
        typography = BmuTypography,
        content = content,
    )
}
```

- [ ] **Step 4: Create SharedBridge.kt**

```kotlin
package com.kxkm.bmu.util

import androidx.compose.material.icons.Icons
import androidx.compose.material.icons.filled.Bolt
import androidx.compose.material.icons.filled.Cloud
import androidx.compose.material.icons.filled.CloudOff
import androidx.compose.material.icons.filled.Lock
import androidx.compose.material.icons.filled.QuestionMark
import androidx.compose.material.icons.filled.Refresh
import androidx.compose.material.icons.filled.Warning
import androidx.compose.material.icons.filled.Wifi
import androidx.compose.material.icons.outlined.BoltOutlined
import androidx.compose.ui.graphics.Color
import androidx.compose.ui.graphics.vector.ImageVector
import com.kxkm.bmu.shared.model.BatteryStatus
import com.kxkm.bmu.shared.model.TransportChannel
import com.kxkm.bmu.shared.model.UserRole
import com.kxkm.bmu.ui.theme.BatteryConnected
import com.kxkm.bmu.ui.theme.BatteryDisconnected
import com.kxkm.bmu.ui.theme.BatteryError
import com.kxkm.bmu.ui.theme.BatteryLocked
import com.kxkm.bmu.ui.theme.BatteryReconnecting

// MARK: - BatteryStatus extensions

val BatteryStatus.displayName: String
    get() = when (this) {
        BatteryStatus.CONNECTED -> "Connecté"
        BatteryStatus.DISCONNECTED -> "Déconnecté"
        BatteryStatus.RECONNECTING -> "Reconnexion"
        BatteryStatus.ERROR -> "Erreur"
        BatteryStatus.LOCKED -> "Verrouillé"
    }

val BatteryStatus.color: Color
    get() = when (this) {
        BatteryStatus.CONNECTED -> BatteryConnected
        BatteryStatus.DISCONNECTED -> BatteryDisconnected
        BatteryStatus.RECONNECTING -> BatteryReconnecting
        BatteryStatus.ERROR -> BatteryError
        BatteryStatus.LOCKED -> BatteryLocked
    }

val BatteryStatus.icon: ImageVector
    get() = when (this) {
        BatteryStatus.CONNECTED -> Icons.Filled.Bolt
        BatteryStatus.DISCONNECTED -> Icons.Outlined.BoltOutlined
        BatteryStatus.RECONNECTING -> Icons.Filled.Refresh
        BatteryStatus.ERROR -> Icons.Filled.Warning
        BatteryStatus.LOCKED -> Icons.Filled.Lock
    }

// MARK: - UserRole extensions

val UserRole.displayName: String
    get() = when (this) {
        UserRole.ADMIN -> "Admin"
        UserRole.TECHNICIAN -> "Technicien"
        UserRole.VIEWER -> "Lecteur"
    }

val UserRole.canControl: Boolean
    get() = this == UserRole.ADMIN || this == UserRole.TECHNICIAN
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
