KomplexKapharnaum/KXKM_Batterie_Parallelator/docs/superpowers/plans/2026-04-02-qa-cicd.md

# QA CI/CD Implementation Plan

> **For agentic workers:** REQUIRED SUB-SKILL: Use superpowers:subagent-driven-development (recommended) or superpowers:executing-plans to implement this plan task-by-task. Steps use checkbox (`- [ ]`) syntax for tracking.

**Goal:** Modernize CI/CD pipeline for the ESP-IDF firmware (active codebase), add host-testable unit tests for new components (VRM, BLE Victron, config labels, VE.Direct parsing), enforce build gates on PRs, and add static analysis.

**Architecture:** Host-compiled Unity tests in `firmware-idf/test/` (no hardware needed). ESP-IDF build gate via GitHub Actions with espressif/idf:v5.4 container. Memory budget enforcement. Clang-tidy for static analysis on display/config code. PR merge requires all gates green.

**Tech Stack:** ESP-IDF v5.4, Unity test framework, GitHub Actions, espressif/idf Docker, clang (host compiler for tests)

**Spec:** Audit findings from 2026-04-02 session

---

## File Structure

| File | Action | Responsibility |
|---|---|---|
| `.github/workflows/esp-idf-ci.yml` | Rewrite | ESP-IDF build + host tests + memory gate |
| `firmware-idf/test/test_vrm_topics/main/test_vrm_topics.cpp` | Create | VRM MQTT topic/payload format validation |
| `firmware-idf/test/test_vrm_topics/CMakeLists.txt` | Create | Test build config |
| `firmware-idf/test/test_ble_victron/main/test_ble_victron.cpp` | Create | BLE Instant Readout payload encoding |
| `firmware-idf/test/test_ble_victron/CMakeLists.txt` | Create | Test build config |
| `firmware-idf/test/test_config_labels/main/test_config_labels.cpp` | Create | Battery label parsing, bounds, persistence format |
| `firmware-idf/test/test_config_labels/CMakeLists.txt` | Create | Test build config |
| `firmware-idf/test/test_vedirect_parser/main/test_vedirect_parser.cpp` | Create | VE.Direct TEXT protocol parsing + checksum |
| `firmware-idf/test/test_vedirect_parser/CMakeLists.txt` | Create | Test build config |
| `firmware-idf/test/Makefile` | Create | Host-compile all tests with g++ |
| `scripts/ci/esp-idf-host-tests.sh` | Create | Run all ESP-IDF host tests |
| `scripts/ci/esp-idf-memory-budget.sh` | Create | Parse idf.py build output for size gate |

---

### Task 1: VRM topic format tests

**Files:**
- Create: `firmware-idf/test/test_vrm_topics/main/test_vrm_topics.cpp`
- Create: `firmware-idf/test/test_vrm_topics/CMakeLists.txt`

Tests the VRM MQTT topic generation and JSON payload format without network. Extracts the pure formatting logic.

- [ ] **Step 1: Create test file**

Create `firmware-idf/test/test_vrm_topics/main/test_vrm_topics.cpp`:

```cpp
/**
 * @file test_vrm_topics.cpp
 * @brief Host tests for VRM MQTT topic/payload formatting.
 * Compile: g++ -Wall -Wextra -DNATIVE_TEST -I. -o test_vrm_topics test_vrm_topics.cpp unity.c
 */
#ifdef NATIVE_TEST

#include "unity.h"
#include <cstdio>
#include <cstring>
#include <cmath>

/* ── Extracted formatting functions (mirror bmu_vrm.cpp logic) ──── */

static void vrm_format_topic(char *buf, size_t len, const char *portal_id, const char *path)
{
    snprintf(buf, len, "N/%s/%s", portal_id, path);
}

static void vrm_format_float(char *buf, size_t len, float val)
{
    snprintf(buf, len, "{\"value\":%.2f}", val);
}

static void vrm_format_int(char *buf, size_t len, int val)
{
    snprintf(buf, len, "{\"value\":%d}", val);
}

static void vrm_format_str(char *buf, size_t len, const char *val)
{
    snprintf(buf, len, "{\"value\":\"%s\"}", val);
}

static float estimate_soc(float avg_v, float v_min, float v_max)
{
    float soc = (avg_v - v_min) / (v_max - v_min) * 100.0f;
    if (soc < 0) soc = 0;
    if (soc > 100) soc = 100;
    return soc;
}

/* ── Tests ────────────────────────────────────────────────────────── */

void test_vrm_topic_solar_voltage(void)
{
    char topic[128];
    vrm_format_topic(topic, sizeof(topic), "70b3d549969af37b", "solarcharger/0/Pv/V");
    TEST_ASSERT_EQUAL_STRING("N/70b3d549969af37b/solarcharger/0/Pv/V", topic);
}

void test_vrm_topic_battery_soc(void)
{
    char topic[128];
    vrm_format_topic(topic, sizeof(topic), "70b3d549969af37b", "battery/0/Soc");
    TEST_ASSERT_EQUAL_STRING("N/70b3d549969af37b/battery/0/Soc", topic);
}

void test_vrm_topic_keepalive(void)
{
    char topic[64];
    snprintf(topic, sizeof(topic), "R/%s/keepalive", "70b3d549969af37b");
    TEST_ASSERT_EQUAL_STRING("R/70b3d549969af37b/keepalive", topic);
}

void test_vrm_payload_float(void)
{
    char json[32];
    vrm_format_float(json, sizeof(json), 26.85f);
    TEST_ASSERT_EQUAL_STRING("{\"value\":26.85}", json);
}

void test_vrm_payload_int(void)
{
    char json[32];
    vrm_format_int(json, sizeof(json), 340);
    TEST_ASSERT_EQUAL_STRING("{\"value\":340}", json);
}

void test_vrm_payload_str(void)
{
    char json[64];
    vrm_format_str(json, sizeof(json), "SmartSolar 150/35");
    TEST_ASSERT_EQUAL_STRING("{\"value\":\"SmartSolar 150/35\"}", json);
}

void test_soc_estimation_midrange(void)
{
    float soc = estimate_soc(26.4f, 24.0f, 28.8f);
    TEST_ASSERT_FLOAT_WITHIN(0.5f, 50.0f, soc);
}

void test_soc_estimation_full(void)
{
    float soc = estimate_soc(28.8f, 24.0f, 28.8f);
    TEST_ASSERT_FLOAT_WITHIN(0.1f, 100.0f, soc);
}

void test_soc_estimation_empty(void)
{
    float soc = estimate_soc(24.0f, 24.0f, 28.8f);
    TEST_ASSERT_FLOAT_WITHIN(0.1f, 0.0f, soc);
}

void test_soc_estimation_clamp_below(void)
{
    float soc = estimate_soc(22.0f, 24.0f, 28.8f);
    TEST_ASSERT_FLOAT_WITHIN(0.1f, 0.0f, soc);
}

void test_soc_estimation_clamp_above(void)
{
    float soc = estimate_soc(32.0f, 24.0f, 28.8f);
    TEST_ASSERT_FLOAT_WITHIN(0.1f, 100.0f, soc);
}

int main(void)
{
    UNITY_BEGIN();
    RUN_TEST(test_vrm_topic_solar_voltage);
    RUN_TEST(test_vrm_topic_battery_soc);
    RUN_TEST(test_vrm_topic_keepalive);
    RUN_TEST(test_vrm_payload_float);
    RUN_TEST(test_vrm_payload_int);
    RUN_TEST(test_vrm_payload_str);
    RUN_TEST(test_soc_estimation_midrange);
    RUN_TEST(test_soc_estimation_full);
    RUN_TEST(test_soc_estimation_empty);
    RUN_TEST(test_soc_estimation_clamp_below);
    RUN_TEST(test_soc_estimation_clamp_above);
    return UNITY_END();
}

#endif /* NATIVE_TEST */
```

- [ ] **Step 2: Create CMakeLists.txt**

Create `firmware-idf/test/test_vrm_topics/CMakeLists.txt`:

```cmake
cmake_minimum_required(VERSION 3.16)
project(test_vrm_topics)
add_executable(test_vrm_topics main/test_vrm_topics.cpp ${UNITY_SRC}/unity.c)
target_compile_definitions(test_vrm_topics PRIVATE NATIVE_TEST)
target_include_directories(test_vrm_topics PRIVATE ${UNITY_SRC})
```

- [ ] **Step 3: Commit**

```bash
git add firmware-idf/test/test_vrm_topics/
git commit -m "test(vrm): host tests for topic format + SOC estimation"
```

---

### Task 2: BLE Victron payload tests

**Files:**
- Create: `firmware-idf/test/test_ble_victron/main/test_ble_victron.cpp`
- Create: `firmware-idf/test/test_ble_victron/CMakeLists.txt`

Tests the BLE advertising payload encoding (battery monitor + solar charger records) without BLE stack.

- [ ] **Step 1: Create test file**

Create `firmware-idf/test/test_ble_victron/main/test_ble_victron.cpp`:

```cpp
/**
 * @file test_ble_victron.cpp
 * @brief Host tests for Victron BLE Instant Readout payload encoding.
 */
#ifdef NATIVE_TEST

#include "unity.h"
#include <cstdint>
#include <cstring>

#define VICTRON_COMPANY_ID      0x02E1
#define VICTRON_RECORD_SOLAR    0x01
#define VICTRON_RECORD_BATTERY  0x02

/* ── Battery Monitor payload packing (mirrors bmu_ble_victron.cpp) ── */

static int pack_battery_payload(uint8_t *plain, float avg_v, float total_i,
                                float soc, float ah_c, float ah_d)
{
    uint16_t remaining_ah = (uint16_t)(ah_c * 10.0f);
    uint16_t voltage = (uint16_t)(avg_v * 100.0f);
    int16_t current = (int16_t)(total_i * 10.0f);
    uint16_t soc_u16 = (uint16_t)(soc * 10.0f);
    uint16_t consumed_ah = (uint16_t)(ah_d * 10.0f);

    memcpy(plain + 0, &remaining_ah, 2);
    memcpy(plain + 2, &voltage, 2);
    memcpy(plain + 4, &current, 2);
    memcpy(plain + 6, &soc_u16, 2);
    memcpy(plain + 8, &consumed_ah, 2);
    return 10;
}

/* ── Solar Charger payload packing ──────────────────────────────── */

static int pack_solar_payload(uint8_t *plain, uint8_t cs, uint8_t err,
                              uint32_t yield_wh, uint16_t ppv,
                              float ibat, float vbat)
{
    plain[0] = cs;
    plain[1] = err;
    uint16_t yield = (uint16_t)(yield_wh / 10);
    int16_t ibat_i = (int16_t)(ibat * 10.0f);
    uint16_t vbat_u = (uint16_t)(vbat * 100.0f);
    memcpy(plain + 2, &yield, 2);
    memcpy(plain + 4, &ppv, 2);
    memcpy(plain + 6, &ibat_i, 2);
    memcpy(plain + 8, &vbat_u, 2);
    return 10;
}

/* ── Manufacturer data header ───────────────────────────────────── */

static int build_mfr_header(uint8_t *buf, uint8_t record_type, uint16_t counter)
{
    buf[0] = (uint8_t)(VICTRON_COMPANY_ID & 0xFF);
    buf[1] = (uint8_t)(VICTRON_COMPANY_ID >> 8);
    buf[2] = record_type;
    buf[3] = (uint8_t)(counter & 0xFF);
    buf[4] = (uint8_t)(counter >> 8);
    return 5;
}

/* ── Tests ────────────────────────────────────────────────────────── */

void test_battery_payload_size(void)
{
    uint8_t plain[16];
    int len = pack_battery_payload(plain, 26.4f, 4.1f, 50.0f, 12.0f, 8.0f);
    TEST_ASSERT_EQUAL_INT(10, len);
}

void test_battery_payload_voltage_encoding(void)
{
    uint8_t plain[10];
    pack_battery_payload(plain, 26.85f, 0.0f, 0.0f, 0.0f, 0.0f);
    uint16_t voltage;
    memcpy(&voltage, plain + 2, 2);
    TEST_ASSERT_EQUAL_UINT16(2685, voltage); /* 26.85V * 100 */
}

void test_battery_payload_current_signed(void)
{
    uint8_t plain[10];
    pack_battery_payload(plain, 0.0f, -3.5f, 0.0f, 0.0f, 0.0f);
    int16_t current;
    memcpy(&current, plain + 4, 2);
    TEST_ASSERT_EQUAL_INT16(-35, current); /* -3.5A * 10 */
}

void test_solar_payload_size(void)
{
    uint8_t plain[16];
    int len = pack_solar_payload(plain, 5, 0, 1250, 340, 12.3f, 27.1f);
    TEST_ASSERT_EQUAL_INT(10, len);
}

void test_solar_payload_charge_state(void)
{
    uint8_t plain[10];
    pack_solar_payload(plain, 5, 0, 0, 0, 0.0f, 0.0f);
    TEST_ASSERT_EQUAL_UINT8(5, plain[0]); /* Float */
}

void test_solar_payload_yield_encoding(void)
{
    uint8_t plain[10];
    pack_solar_payload(plain, 0, 0, 1250, 0, 0.0f, 0.0f);
    uint16_t yield;
    memcpy(&yield, plain + 2, 2);
    TEST_ASSERT_EQUAL_UINT16(125, yield); /* 1250 Wh / 10 = 125 (0.01 kWh) */
}

void test_mfr_header_company_id(void)
{
    uint8_t buf[8];
    build_mfr_header(buf, VICTRON_RECORD_BATTERY, 42);
    TEST_ASSERT_EQUAL_UINT8(0xE1, buf[0]); /* Company ID LE low byte */
    TEST_ASSERT_EQUAL_UINT8(0x02, buf[1]); /* Company ID LE high byte */
}

void test_mfr_header_record_type(void)
{
    uint8_t buf[8];
    build_mfr_header(buf, VICTRON_RECORD_SOLAR, 0);
    TEST_ASSERT_EQUAL_UINT8(VICTRON_RECORD_SOLAR, buf[2]);
}

void test_mfr_header_counter(void)
{
    uint8_t buf[8];
    build_mfr_header(buf, 0, 0x1234);
    TEST_ASSERT_EQUAL_UINT8(0x34, buf[3]);
    TEST_ASSERT_EQUAL_UINT8(0x12, buf[4]);
}

int main(void)
{
    UNITY_BEGIN();
    RUN_TEST(test_battery_payload_size);
    RUN_TEST(test_battery_payload_voltage_encoding);
    RUN_TEST(test_battery_payload_current_signed);
    RUN_TEST(test_solar_payload_size);
    RUN_TEST(test_solar_payload_charge_state);
    RUN_TEST(test_solar_payload_yield_encoding);
    RUN_TEST(test_mfr_header_company_id);
    RUN_TEST(test_mfr_header_record_type);
    RUN_TEST(test_mfr_header_counter);
    return UNITY_END();
}

#endif
```

- [ ] **Step 2: Create CMakeLists.txt**

Create `firmware-idf/test/test_ble_victron/CMakeLists.txt`:

```cmake
cmake_minimum_required(VERSION 3.16)
project(test_ble_victron)
add_executable(test_ble_victron main/test_ble_victron.cpp ${UNITY_SRC}/unity.c)
target_compile_definitions(test_ble_victron PRIVATE NATIVE_TEST)
target_include_directories(test_ble_victron PRIVATE ${UNITY_SRC})
```

- [ ] **Step 3: Commit**

```bash
git add firmware-idf/test/test_ble_victron/
git commit -m "test(ble-victron): host tests for Instant Readout payload encoding"
```

---

### Task 3: Config labels tests

**Files:**
- Create: `firmware-idf/test/test_config_labels/main/test_config_labels.cpp`
- Create: `firmware-idf/test/test_config_labels/CMakeLists.txt`

Tests battery label parsing, bounds checking, file format generation.

- [ ] **Step 1: Create test file**

Create `firmware-idf/test/test_config_labels/main/test_config_labels.cpp`:

```cpp
/**
 * @file test_config_labels.cpp
 * @brief Host tests for battery label config: bounds, truncation, file format.
 */
#ifdef NATIVE_TEST

#include "unity.h"
#include <cstring>
#include <cstdio>

#define BMU_MAX_BATTERIES       16
#define BMU_CONFIG_BATLABEL_MAX  9

/* ── Simulated label storage (mirrors bmu_config.cpp) ────────────── */

static char s_labels[BMU_MAX_BATTERIES][BMU_CONFIG_BATLABEL_MAX];

static void init_defaults(void)
{
    for (int i = 0; i < BMU_MAX_BATTERIES; i++) {
        snprintf(s_labels[i], BMU_CONFIG_BATLABEL_MAX, "B%d", i + 1);
    }
}

static int set_label(int idx, const char *label)
{
    if (idx < 0 || idx >= BMU_MAX_BATTERIES) return -1;
    if (label == NULL || label[0] == '\0') return -1;
    strncpy(s_labels[idx], label, BMU_CONFIG_BATLABEL_MAX - 1);
    s_labels[idx][BMU_CONFIG_BATLABEL_MAX - 1] = '\0';
    return 0;
}

static const char *get_label(int idx)
{
    if (idx < 0 || idx >= BMU_MAX_BATTERIES) return "?";
    return s_labels[idx];
}

/* Parse file content (one label per line) into label storage */
static int parse_labels_from_buffer(const char *buf)
{
    init_defaults();
    int idx = 0;
    const char *p = buf;
    while (idx < BMU_MAX_BATTERIES && *p != '\0') {
        const char *eol = strchr(p, '\n');
        if (eol == NULL) eol = p + strlen(p);
        int len = (int)(eol - p);
        /* Strip \r */
        if (len > 0 && *(eol - 1) == '\r') len--;
        if (len > 0) {
            if (len > BMU_CONFIG_BATLABEL_MAX - 1) len = BMU_CONFIG_BATLABEL_MAX - 1;
            memcpy(s_labels[idx], p, len);
            s_labels[idx][len] = '\0';
        }
        idx++;
        p = (*eol == '\n') ? eol + 1 : eol;
    }
    return idx;
}

/* ── Tests ────────────────────────────────────────────────────────── */

void test_defaults(void)
{
    init_defaults();
    TEST_ASSERT_EQUAL_STRING("B1", get_label(0));
    TEST_ASSERT_EQUAL_STRING("B16", get_label(15));
}

void test_set_valid(void)
{
    init_defaults();
    TEST_ASSERT_EQUAL_INT(0, set_label(0, "Tender"));
    TEST_ASSERT_EQUAL_STRING("Tender", get_label(0));
}

void test_set_truncation(void)
{
    init_defaults();
    set_label(0, "VeryLongBatteryName");
    TEST_ASSERT_EQUAL_INT(8, (int)strlen(get_label(0)));
}

void test_set_invalid_idx_negative(void)
{
    TEST_ASSERT_EQUAL_INT(-1, set_label(-1, "X"));
}

void test_set_invalid_idx_overflow(void)
{
    TEST_ASSERT_EQUAL_INT(-1, set_label(16, "X"));
}

void test_set_empty_label(void)
{
    TEST_ASSERT_EQUAL_INT(-1, set_label(0, ""));
}

void test_set_null_label(void)
{
    TEST_ASSERT_EQUAL_INT(-1, set_label(0, NULL));
}

void test_get_invalid_idx(void)
{
    TEST_ASSERT_EQUAL_STRING("?", get_label(-1));
    TEST_ASSERT_EQUAL_STRING("?", get_label(16));
}

void test_parse_file_basic(void)
{
    int n = parse_labels_from_buffer("Tender\nLED1\nLED2\nCabine\n");
    TEST_ASSERT_EQUAL_INT(4, n);
    TEST_ASSERT_EQUAL_STRING("Tender", get_label(0));
    TEST_ASSERT_EQUAL_STRING("LED1", get_label(1));
    TEST_ASSERT_EQUAL_STRING("LED2", get_label(2));
    TEST_ASSERT_EQUAL_STRING("Cabine", get_label(3));
    TEST_ASSERT_EQUAL_STRING("B5", get_label(4)); /* default kept */
}

void test_parse_file_empty_lines(void)
{
    parse_labels_from_buffer("Tender\n\nLED2\n");
    TEST_ASSERT_EQUAL_STRING("Tender", get_label(0));
    TEST_ASSERT_EQUAL_STRING("B2", get_label(1)); /* empty = keep default */
    TEST_ASSERT_EQUAL_STRING("LED2", get_label(2));
}

void test_parse_file_crlf(void)
{
    parse_labels_from_buffer("Tender\r\nLED1\r\n");
    TEST_ASSERT_EQUAL_STRING("Tender", get_label(0));
    TEST_ASSERT_EQUAL_STRING("LED1", get_label(1));
}

void test_parse_file_overflow(void)
{
    /* More than 16 lines — extra ignored */
    char buf[512] = {};
    for (int i = 0; i < 20; i++) {
        char line[16];
        snprintf(line, sizeof(line), "BAT%d\n", i);
        strcat(buf, line);
    }
    int n = parse_labels_from_buffer(buf);
    TEST_ASSERT_EQUAL_INT(16, n); /* capped */
}

int main(void)
{
    UNITY_BEGIN();
    RUN_TEST(test_defaults);
    RUN_TEST(test_set_valid);
    RUN_TEST(test_set_truncation);
    RUN_TEST(test_set_invalid_idx_negative);
    RUN_TEST(test_set_invalid_idx_overflow);
    RUN_TEST(test_set_empty_label);
    RUN_TEST(test_set_null_label);
    RUN_TEST(test_get_invalid_idx);
    RUN_TEST(test_parse_file_basic);
    RUN_TEST(test_parse_file_empty_lines);
    RUN_TEST(test_parse_file_crlf);
    RUN_TEST(test_parse_file_overflow);
    return UNITY_END();
}

#endif
```

- [ ] **Step 2: Create CMakeLists.txt**

Create `firmware-idf/test/test_config_labels/CMakeLists.txt`:

```cmake
cmake_minimum_required(VERSION 3.16)
project(test_config_labels)
add_executable(test_config_labels main/test_config_labels.cpp ${UNITY_SRC}/unity.c)
target_compile_definitions(test_config_labels PRIVATE NATIVE_TEST)
target_include_directories(test_config_labels PRIVATE ${UNITY_SRC})
```

- [ ] **Step 3: Commit**

```bash
git add firmware-idf/test/test_config_labels/
git commit -m "test(config): host tests for battery label parsing + bounds"
```

---

### Task 4: VE.Direct parser tests

**Files:**
- Create: `firmware-idf/test/test_vedirect_parser/main/test_vedirect_parser.cpp`
- Create: `firmware-idf/test/test_vedirect_parser/CMakeLists.txt`

Tests VE.Direct TEXT protocol parsing + checksum validation without UART.

- [ ] **Step 1: Create test file**

Create `firmware-idf/test/test_vedirect_parser/main/test_vedirect_parser.cpp`:

```cpp
/**
 * @file test_vedirect_parser.cpp
 * @brief Host tests for VE.Direct TEXT protocol parsing + checksum.
 */
#ifdef NATIVE_TEST

#include "unity.h"
#include <cstring>
#include <cstdio>
#include <cstdlib>

/* ── Simulated parser state (mirrors bmu_vedirect.cpp) ───────────── */

typedef struct {
    float    battery_voltage_v;
    float    battery_current_a;
    float    panel_voltage_v;
    uint16_t panel_power_w;
    uint8_t  charge_state;
    uint8_t  error_code;
    uint32_t yield_today_wh;
    bool     valid;
} vedirect_data_t;

static vedirect_data_t s_data;

/* Parse a single label=value pair */
static void parse_field(const char *label, const char *value)
{
    if (strcmp(label, "V") == 0) {
        s_data.battery_voltage_v = atof(value) / 1000.0f;
    } else if (strcmp(label, "I") == 0) {
        s_data.battery_current_a = atof(value) / 1000.0f;
    } else if (strcmp(label, "VPV") == 0) {
        s_data.panel_voltage_v = atof(value) / 1000.0f;
    } else if (strcmp(label, "PPV") == 0) {
        s_data.panel_power_w = (uint16_t)atoi(value);
    } else if (strcmp(label, "CS") == 0) {
        s_data.charge_state = (uint8_t)atoi(value);
    } else if (strcmp(label, "ERR") == 0) {
        s_data.error_code = (uint8_t)atoi(value);
    } else if (strcmp(label, "H20") == 0) {
        s_data.yield_today_wh = (uint32_t)(atoi(value) * 10);
    }
}

/* Validate VE.Direct checksum: sum of all bytes in frame must = 0 (mod 256) */
static bool validate_checksum(const char *frame, int len)
{
    uint8_t sum = 0;
    for (int i = 0; i < len; i++) {
        sum += (uint8_t)frame[i];
    }
    return (sum == 0);
}

/* Parse a complete TEXT frame (multiple lines terminated by Checksum) */
static bool parse_frame(const char *frame)
{
    memset(&s_data, 0, sizeof(s_data));
    const char *p = frame;

    while (*p) {
        /* Find tab separator */
        const char *tab = strchr(p, '\t');
        if (!tab) break;

        /* Extract label */
        char label[16] = {};
        int llen = (int)(tab - p);
        if (llen > 15) llen = 15;
        memcpy(label, p, llen);

        /* Find end of line */
        const char *eol = strchr(tab + 1, '\r');
        if (!eol) eol = strchr(tab + 1, '\n');
        if (!eol) eol = tab + 1 + strlen(tab + 1);

        /* Extract value */
        char value[32] = {};
        int vlen = (int)(eol - tab - 1);
        if (vlen > 31) vlen = 31;
        memcpy(value, tab + 1, vlen);

        if (strcmp(label, "Checksum") != 0) {
            parse_field(label, value);
        }

        /* Skip to next line */
        p = eol;
        while (*p == '\r' || *p == '\n') p++;
    }

    s_data.valid = true;
    return true;
}

/* ── Tests ────────────────────────────────────────────────────────── */

void test_parse_voltage(void)
{
    parse_frame("V\t27140\r\n");
    TEST_ASSERT_FLOAT_WITHIN(0.01f, 27.14f, s_data.battery_voltage_v);
}

void test_parse_current_positive(void)
{
    parse_frame("I\t12300\r\n");
    TEST_ASSERT_FLOAT_WITHIN(0.01f, 12.3f, s_data.battery_current_a);
}

void test_parse_current_negative(void)
{
    parse_frame("I\t-500\r\n");
    TEST_ASSERT_FLOAT_WITHIN(0.01f, -0.5f, s_data.battery_current_a);
}

void test_parse_panel_voltage(void)
{
    parse_frame("VPV\t45200\r\n");
    TEST_ASSERT_FLOAT_WITHIN(0.01f, 45.2f, s_data.panel_voltage_v);
}

void test_parse_panel_power(void)
{
    parse_frame("PPV\t340\r\n");
    TEST_ASSERT_EQUAL_UINT16(340, s_data.panel_power_w);
}

void test_parse_charge_state_float(void)
{
    parse_frame("CS\t5\r\n");
    TEST_ASSERT_EQUAL_UINT8(5, s_data.charge_state);
}

void test_parse_yield_today(void)
{
    parse_frame("H20\t125\r\n");
    TEST_ASSERT_EQUAL_UINT32(1250, s_data.yield_today_wh); /* 125 * 10 = 1250 Wh */
}

void test_parse_multi_field_frame(void)
{
    parse_frame(
        "V\t27140\r\n"
        "I\t12300\r\n"
        "VPV\t45200\r\n"
        "PPV\t340\r\n"
        "CS\t5\r\n"
        "ERR\t0\r\n"
        "H20\t125\r\n"
    );
    TEST_ASSERT_FLOAT_WITHIN(0.01f, 27.14f, s_data.battery_voltage_v);
    TEST_ASSERT_FLOAT_WITHIN(0.01f, 12.3f, s_data.battery_current_a);
    TEST_ASSERT_FLOAT_WITHIN(0.01f, 45.2f, s_data.panel_voltage_v);
    TEST_ASSERT_EQUAL_UINT16(340, s_data.panel_power_w);
    TEST_ASSERT_EQUAL_UINT8(5, s_data.charge_state);
    TEST_ASSERT_EQUAL_UINT8(0, s_data.error_code);
    TEST_ASSERT_EQUAL_UINT32(1250, s_data.yield_today_wh);
}

void test_checksum_valid(void)
{
    /* Real VE.Direct frame: sum of all bytes = 0 mod 256 */
    /* Simplified: "A\t1\r\nChecksum\t\xfe" → 'A'+'\t'+'1'+'\r'+'\n'+'C'...'m'+'\t'+0xFE */
    /* For simplicity, test the checksum logic directly */
    uint8_t frame[] = { 0x41, 0x09, 0x31, 0x0D, 0x0A }; /* "A\t1\r\n" */
    uint8_t sum = 0;
    for (int i = 0; i < 5; i++) sum += frame[i];
    uint8_t checksum_byte = (uint8_t)(0 - sum); /* byte that makes sum = 0 */
    uint8_t full[6];
    memcpy(full, frame, 5);
    full[5] = checksum_byte;
    TEST_ASSERT_TRUE(validate_checksum((const char *)full, 6));
}

void test_checksum_invalid(void)
{
    uint8_t frame[] = { 0x41, 0x09, 0x31, 0x0D, 0x0A, 0x00 };
    TEST_ASSERT_FALSE(validate_checksum((const char *)frame, 6));
}

int main(void)
{
    UNITY_BEGIN();
    RUN_TEST(test_parse_voltage);
    RUN_TEST(test_parse_current_positive);
    RUN_TEST(test_parse_current_negative);
    RUN_TEST(test_parse_panel_voltage);
    RUN_TEST(test_parse_panel_power);
    RUN_TEST(test_parse_charge_state_float);
    RUN_TEST(test_parse_yield_today);
    RUN_TEST(test_parse_multi_field_frame);
    RUN_TEST(test_checksum_valid);
    RUN_TEST(test_checksum_invalid);
    return UNITY_END();
}

#endif
```

- [ ] **Step 2: Create CMakeLists.txt**

Create `firmware-idf/test/test_vedirect_parser/CMakeLists.txt`:

```cmake
cmake_minimum_required(VERSION 3.16)
project(test_vedirect_parser)
add_executable(test_vedirect_parser main/test_vedirect_parser.cpp ${UNITY_SRC}/unity.c)
target_compile_definitions(test_vedirect_parser PRIVATE NATIVE_TEST)
target_include_directories(test_vedirect_parser PRIVATE ${UNITY_SRC})
```

- [ ] **Step 3: Commit**

```bash
git add firmware-idf/test/test_vedirect_parser/
git commit -m "test(vedirect): host tests for TEXT protocol parsing + checksum"
```

---

### Task 5: Host test runner Makefile + script

**Files:**
- Create: `firmware-idf/test/Makefile`
- Create: `scripts/ci/esp-idf-host-tests.sh`

Unified build+run for all host tests. Downloads Unity if needed.

- [ ] **Step 1: Create Makefile**

Create `firmware-idf/test/Makefile`:

```makefile
# Host-compiled Unity tests for ESP-IDF firmware
# Usage: make all  (or make test_vrm_topics, etc.)

CXX      ?= g++
CXXFLAGS  = -Wall -Wextra -DNATIVE_TEST -std=c++17
UNITY_DIR = unity
UNITY_SRC = $(UNITY_DIR)/unity.c
UNITY_INC = -I$(UNITY_DIR)

TESTS = test_protection test_vrm_topics test_ble_victron test_config_labels test_vedirect_parser

.PHONY: all clean download_unity run

all: download_unity $(TESTS) run

download_unity:
	@if [ ! -f $(UNITY_DIR)/unity.h ]; then \
		echo "Downloading Unity..."; \
		mkdir -p $(UNITY_DIR); \
		curl -sL https://raw.githubusercontent.com/ThrowTheSwitch/Unity/v2.6.1/src/unity.h -o $(UNITY_DIR)/unity.h; \
		curl -sL https://raw.githubusercontent.com/ThrowTheSwitch/Unity/v2.6.1/src/unity.c -o $(UNITY_DIR)/unity.c; \
		curl -sL https://raw.githubusercontent.com/ThrowTheSwitch/Unity/v2.6.1/src/unity_internals.h -o $(UNITY_DIR)/unity_internals.h; \
	fi

test_protection: download_unity
	$(CXX) $(CXXFLAGS) $(UNITY_INC) -o $@ test_protection/main/test_protection.cpp $(UNITY_SRC)

test_vrm_topics: download_unity
	$(CXX) $(CXXFLAGS) $(UNITY_INC) -o $@ test_vrm_topics/main/test_vrm_topics.cpp $(UNITY_SRC)

test_ble_victron: download_unity
	$(CXX) $(CXXFLAGS) $(UNITY_INC) -o $@ test_ble_victron/main/test_ble_victron.cpp $(UNITY_SRC)

test_config_labels: download_unity
	$(CXX) $(CXXFLAGS) $(UNITY_INC) -o $@ test_config_labels/main/test_config_labels.cpp $(UNITY_SRC)

test_vedirect_parser: download_unity
	$(CXX) $(CXXFLAGS) $(UNITY_INC) -o $@ test_vedirect_parser/main/test_vedirect_parser.cpp $(UNITY_SRC)

run: $(TESTS)
	@echo "=== Running all host tests ==="
	@failed=0; \
	for t in $(TESTS); do \
		echo "--- $$t ---"; \
		./$$t || failed=1; \
	done; \
	if [ $$failed -ne 0 ]; then echo "SOME TESTS FAILED"; exit 1; fi
	@echo "=== All tests passed ==="

clean:
	rm -f $(TESTS)
```

- [ ] **Step 2: Create CI script**

Create `scripts/ci/esp-idf-host-tests.sh`:

```bash
#!/usr/bin/env bash
set -euo pipefail

echo "=== ESP-IDF Host Tests ==="

cd "$(dirname "$0")/../../firmware-idf/test"

make clean
make all

echo "=== All ESP-IDF host tests passed ==="
```

Make it executable:

```bash
chmod +x scripts/ci/esp-idf-host-tests.sh
```

- [ ] **Step 3: Commit**

```bash
git add firmware-idf/test/Makefile scripts/ci/esp-idf-host-tests.sh
git commit -m "ci: host test runner Makefile + script for ESP-IDF tests"
```

---

### Task 6: ESP-IDF memory budget script

**Files:**
- Create: `scripts/ci/esp-idf-memory-budget.sh`

Parses `idf.py size` output and fails if app exceeds partition size threshold.

- [ ] **Step 1: Create script**

Create `scripts/ci/esp-idf-memory-budget.sh`:

```bash
#!/usr/bin/env bash
set -euo pipefail

# ESP-IDF memory budget gate
# Usage: esp-idf-memory-budget.sh [--flash-max 85]
#
# Checks binary size vs OTA partition (2MB = 0x200000)

FLASH_MAX=${1:-85}
PARTITION_SIZE=$((0x200000))  # 2MB OTA partition

cd "$(dirname "$0")/../../firmware-idf"

echo "=== ESP-IDF Memory Budget Check ==="

# Get binary size
BIN="build/kxkm-bmu.bin"
if [ ! -f "$BIN" ]; then
    echo "ERROR: $BIN not found. Run 'idf.py build' first."
    exit 1
fi

BIN_SIZE=$(stat -f%z "$BIN" 2>/dev/null || stat -c%s "$BIN" 2>/dev/null)
PERCENT=$(( BIN_SIZE * 100 / PARTITION_SIZE ))

echo "Binary: $BIN_SIZE bytes ($PERCENT% of ${PARTITION_SIZE} byte partition)"
echo "Threshold: ${FLASH_MAX}%"

if [ "$PERCENT" -gt "$FLASH_MAX" ]; then
    echo "FAIL: Flash usage ${PERCENT}% exceeds max ${FLASH_MAX}%"
    exit 1
fi

echo "PASS: Flash usage ${PERCENT}% <= ${FLASH_MAX}%"

# RAM check via idf.py size (if available)
if command -v idf.py &>/dev/null; then
    echo ""
    idf.py size 2>/dev/null | grep -E "Total|Used|Available|DRAM" || true
fi

echo "=== Memory budget OK ==="
```

Make executable:

```bash
chmod +x scripts/ci/esp-idf-memory-budget.sh
```

- [ ] **Step 2: Commit**

```bash
git add scripts/ci/esp-idf-memory-budget.sh
git commit -m "ci: ESP-IDF memory budget gate script"
```

---

### Task 7: Rewrite esp-idf-ci.yml — unified pipeline

**Files:**
- Rewrite: `.github/workflows/esp-idf-ci.yml`

3 jobs: host-tests, build, memory-budget. Triggers on push to main + PRs + victron branch.

- [ ] **Step 1: Rewrite workflow**

Rewrite `.github/workflows/esp-idf-ci.yml`:

```yaml
name: ESP-IDF CI

on:
  push:
    branches: [main, victron]
    paths: ['firmware-idf/**', '.github/workflows/esp-idf-ci.yml']
  pull_request:
    paths: ['firmware-idf/**']
  workflow_dispatch:

concurrency:
  group: ${{ github.workflow }}-${{ github.ref }}
  cancel-in-progress: true

jobs:
  host-tests:
    name: Host Tests (Unity)
    runs-on: ubuntu-latest
    timeout-minutes: 5
    steps:
      - uses: actions/checkout@v4
      - name: Run host tests
        run: |
          cd firmware-idf/test
          make all

  build:
    name: ESP-IDF Build (v5.4)
    runs-on: ubuntu-latest
    container: espressif/idf:v5.4
    timeout-minutes: 20
    steps:
      - uses: actions/checkout@v4
        with:
          submodules: recursive
      - name: Build firmware
        run: |
          cd firmware-idf
          idf.py set-target esp32s3
          idf.py build
      - name: Upload binary
        uses: actions/upload-artifact@v4
        with:
          name: kxkm-bmu-firmware
          path: |
            firmware-idf/build/kxkm-bmu.bin
            firmware-idf/build/bootloader/bootloader.bin
            firmware-idf/build/partition_table/partition-table.bin

  memory-budget:
    name: Memory Budget Gate
    needs: build
    runs-on: ubuntu-latest
    timeout-minutes: 5
    steps:
      - uses: actions/checkout@v4
      - uses: actions/download-artifact@v4
        with:
          name: kxkm-bmu-firmware
          path: firmware-idf/build/
      - name: Check binary size
        run: |
          BIN="firmware-idf/build/kxkm-bmu.bin"
          PARTITION_SIZE=$((0x200000))
          BIN_SIZE=$(stat -c%s "$BIN")
          PERCENT=$(( BIN_SIZE * 100 / PARTITION_SIZE ))
          echo "Binary: $BIN_SIZE bytes ($PERCENT% of 2MB partition)"
          if [ "$PERCENT" -gt 85 ]; then
            echo "::error::Flash usage ${PERCENT}% exceeds 85% threshold"
            exit 1
          fi
          echo "✅ Flash: ${PERCENT}% (max 85%)"
```

- [ ] **Step 2: Commit**

```bash
git add .github/workflows/esp-idf-ci.yml
git commit -m "ci: rewrite ESP-IDF pipeline — host tests + build v5.4 + memory gate"
```

---

### Task 8: Integration — verify full pipeline locally

**Files:** None (verification only)

- [ ] **Step 1: Run host tests locally**

```bash
cd firmware-idf/test && make clean && make all
```

Expected: 5 test suites, all passing (protection + vrm + ble + labels + vedirect)

- [ ] **Step 2: Build ESP-IDF**

```bash
cd firmware-idf && idf.py build 2>&1 | tail -5
```

Expected: `Project build complete`

- [ ] **Step 3: Run memory budget**

```bash
scripts/ci/esp-idf-memory-budget.sh
```

Expected: `PASS: Flash usage XX% <= 85%`

- [ ] **Step 4: Push and verify GitHub Actions**

```bash
git push origin victron
```

Check `https://github.com/KomplexKapharnaum/KXKM_Batterie_Parallelator/actions` — all 3 jobs should pass.

- [ ] **Step 5: Commit**

```bash
git add -A
git commit -m "ci: QA pipeline verified — 5 test suites + build + memory gate"
```
