KomplexKapharnaum/KXKM_Batterie_Parallelator/firmware-idf/components/bmu_protection/include/bmu_protection.h

#pragma once

#include "bmu_types.h"
#include "bmu_ina237.h"
#include "bmu_tca9535.h"
#include "bmu_config.h"
#include "esp_err.h"
#include "freertos/FreeRTOS.h"
#include "freertos/semphr.h"
#include "freertos/queue.h"
#include "freertos/task.h"

#ifdef __cplusplus
extern "C" {
#endif

// bmu_battery_state_t now defined in bmu_types.h

// Queue configuration for snapshot distribution
typedef struct {
    QueueHandle_t q_balancer;
    QueueHandle_t q_display;
    QueueHandle_t q_cloud;
    QueueHandle_t q_ble;
    QueueHandle_t q_cmd;
} bmu_protection_queues_t;

typedef struct {
    bmu_ina237_t         *ina_devices;
    bmu_tca9535_handle_t *tca_devices;
    uint8_t               nb_ina;
    uint8_t               nb_tca;

    SemaphoreHandle_t     state_mutex;
    float                 battery_voltages[BMU_MAX_BATTERIES];
    float                 battery_currents[BMU_MAX_BATTERIES]; /**< Cached current (A) */
    int                   nb_switch[BMU_MAX_BATTERIES];
    int64_t               reconnect_time_ms[BMU_MAX_BATTERIES];
    bmu_battery_state_t   battery_state[BMU_MAX_BATTERIES];
    uint8_t               imbalance_count[BMU_MAX_BATTERIES]; /**< Consecutive imbalance cycles */
    bmu_device_health_t   ina_health[BMU_MAX_BATTERIES];     /**< Per-INA I2C health score */

    // RTOS task + queue infrastructure
    bmu_protection_queues_t queues;
    uint16_t                cycle_count;
    uint32_t                task_period_ms;
    TaskHandle_t            task_handle;
} bmu_protection_ctx_t;

#define BMU_IMBALANCE_CONFIRM_CYCLES 3  /**< Cycles d'imbalance avant disconnect */

esp_err_t bmu_protection_init(bmu_protection_ctx_t *ctx,
                               bmu_ina237_t *ina, uint8_t nb_ina,
                               bmu_tca9535_handle_t *tca, uint8_t nb_tca);

/**
 * @brief Compute fleet max voltage (CONNECTED batteries only), under mutex.
 * Call once per protection cycle, pass result to check_battery_ex.
 */
float bmu_protection_compute_fleet_max(bmu_protection_ctx_t *ctx);

/**
 * @brief Check battery with pre-computed fleet_max (avoids N recomputations).
 */
esp_err_t bmu_protection_check_battery_ex(bmu_protection_ctx_t *ctx, int battery_idx,
                                           float fleet_max_mv);

esp_err_t bmu_protection_all_off(bmu_protection_ctx_t *ctx);

esp_err_t bmu_protection_reset_switch_count(bmu_protection_ctx_t *ctx, int battery_idx);

bmu_battery_state_t bmu_protection_get_state(bmu_protection_ctx_t *ctx, int battery_idx);

float bmu_protection_get_voltage(bmu_protection_ctx_t *ctx, int battery_idx);
float bmu_protection_get_current(bmu_protection_ctx_t *ctx, int battery_idx);
esp_err_t bmu_protection_get_switch_count(bmu_protection_ctx_t *ctx, int battery_idx,
                                          int *switch_count_out);

/**
 * @brief Web-initiated switch command. Validates voltage precondition before switching.
 * Respects locked batteries — returns ESP_ERR_NOT_ALLOWED for locked batteries.
 */
esp_err_t bmu_protection_web_switch(bmu_protection_ctx_t *ctx, int battery_idx, bool on);

/**
 * @brief Update topology counts after hotplug re-scan.
 * Resets state of new battery slots to DISCONNECTED.
 * Must be called with valid nb_ina <= BMU_MAX_BATTERIES and nb_tca <= BMU_MAX_TCA.
 */
esp_err_t bmu_protection_update_topology(bmu_protection_ctx_t *ctx,
                                          uint8_t new_nb_ina,
                                          uint8_t new_nb_tca);

// ── RTOS queue / task API (Phase 2) ──

esp_err_t bmu_protection_set_queues(bmu_protection_ctx_t *ctx,
                                     const bmu_protection_queues_t *queues);

void bmu_protection_publish_snapshot(bmu_protection_ctx_t *ctx);

void bmu_protection_process_commands(bmu_protection_ctx_t *ctx);

esp_err_t bmu_protection_start_task(bmu_protection_ctx_t *ctx,
                                     uint32_t period_ms,
                                     UBaseType_t priority,
                                     uint32_t stack_size);

#ifdef __cplusplus
}
#endif
