KomplexKapharnaum/KXKM_Batterie_Parallelator/firmware/src/INAHandler.h

/*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
 * You should have received a copy of the GNU General Public License
 * along with this program. If not, see <https://www.gnu.org/licenses/>.
 */

/**
 * @file INAHandler.h
 * @brief Déclaration de la classe INAHandler pour gérer les appareils INA.
 * @details Créé par Clément Saillant pour Komplex Kapharnum assisté par IA.
 */

#ifndef INA_HANDLER_H
#define INA_HANDLER_H

#include <KxLogger.h>
#include <INA226.h>
#include <Wire.h>

/**
 * @class INAHandler
 * @brief Classe pour gérer les appareils INA.
 */
class INAHandler
{
public:
    INAHandler();
    ~INAHandler();
    void begin(const uint8_t amp, const uint16_t micro_ohm);
    void read(const uint8_t deviceNumber);
    float read_current(const uint8_t deviceNumber);
    float read_volt(const uint8_t deviceNumber);
    float read_power(const uint8_t deviceNumber);
    bool read_voltage_current(const uint8_t deviceNumber, float &voltage, float &current);
    void set_max_voltage(const float_t voltage);
    void set_min_voltage(const float_t voltage);
    void set_max_current(const float_t current);
    void set_max_charge_current(const float_t current);
    uint8_t getDeviceAddress(const uint8_t deviceNumber);
    uint8_t getNbINA();
    void setI2CSpeed(int speed);
    int detect_batteries();

private:
    void initialize_ina(const uint8_t deviceNumber, float amp, float shunt_ohm);
    bool isValidIndex(uint8_t deviceNumber) const;
    const int INA_ADDR[16] = {0x40, 0x41, 0x42, 0x43, 0x44, 0x45, 0x46, 0x47, 0x48, 0x49, 0x4A, 0x4B, 0x4C, 0x4D, 0x4E, 0x4F}; ///< Adresses INA
    INA226* sensors[16];                                                                                                       ///< Capteurs INA226 connectes
    volatile uint8_t deviceNumber;                                                                                             ///< Premier capteur detecte
    volatile uint64_t sumBusMillVolts[17];                                                                                     ///< Compat: somme tension bus
    volatile int64_t sumBusMicroAmp[17];                                                                                       ///< Compat: somme courant bus
    volatile uint8_t readings[17];                                                                                             ///< Compat: nombre de mesures
    byte INA_address_connected[16];                                                                                            // Adresses INA connectées
    uint8_t Nb_INA;                                                                                                            // Nombre d'INA connectés
    int max_voltage = 30000;                                                                                                   // Seuil de surtension de la batterie en mV (overvoltage)
    int min_voltage = 24000;                                                                                                   // Seuil de sous-tension de la batterie en mV (undervoltage)
    int max_current = 1000;                                                                                                    // Seuil de surintensité de la batterie en mA
    int max_charge_current = 1000;                                                                                             // Seuil de courant de charge de la batterie en mA
    int i2cSpeedKHz = 100; // Vitesse I2C en KHz
};

#endif // INA_HANDLER_H
