KomplexKapharnaum/KXKM_Batterie_Parallelator/firmware-idf/components/bmu_i2c/include/bmu_i2c.h

#pragma once

#include "driver/i2c_master.h"
#include "esp_err.h"
#include "freertos/FreeRTOS.h"

#ifdef __cplusplus
extern "C" {
#endif

#define BMU_I2C_SDA_GPIO    GPIO_NUM_41
#define BMU_I2C_SCL_GPIO    GPIO_NUM_40
#define BMU_I2C_PORT        I2C_NUM_1
#define BMU_I2C_FREQ_HZ     100000

esp_err_t bmu_i2c_init(i2c_master_bus_handle_t *bus_handle);
esp_err_t bmu_i2c_add_device(i2c_master_bus_handle_t bus, uint8_t addr,
                              i2c_master_dev_handle_t *dev);
esp_err_t bmu_i2c_probe(i2c_master_bus_handle_t bus, uint8_t addr, TickType_t timeout_ticks);
int bmu_i2c_scan(i2c_master_bus_handle_t bus);

/**
 * @brief Acquire the BMU I2C bus mutex. Must be called before multi-register operations.
 * @return ESP_OK if acquired, ESP_ERR_TIMEOUT if not acquired within 100ms.
 */
esp_err_t bmu_i2c_lock(void);

/**
 * @brief Release the BMU I2C bus mutex.
 */
void bmu_i2c_unlock(void);

/**
 * @brief Record a successful I2C operation (resets failure counter).
 */
void bmu_i2c_record_success(void);

/**
 * @brief Record an I2C failure. After 5 consecutive failures, triggers bus recovery.
 */
void bmu_i2c_record_failure(void);

/**
 * @brief I2C bus recovery via i2c_master_bus_reset() (driver ESP-IDF).
 * L'ancien fallback bit-bang a été retiré (il détachait les pins du
 * périphérique I2C et rendait le bus inutilisable après recovery).
 */
esp_err_t bmu_i2c_bus_recover(void);

// Per-device health tracking
#include "bmu_types.h"

void bmu_i2c_health_record_success(bmu_device_health_t *health);
void bmu_i2c_health_record_failure(bmu_device_health_t *health);
bool bmu_i2c_health_is_warn(const bmu_device_health_t *health);
bool bmu_i2c_health_is_critical(const bmu_device_health_t *health);
bool bmu_i2c_health_can_reconnect(const bmu_device_health_t *health);

#ifdef __cplusplus
}
#endif
