KomplexKapharnaum/KXKM_Batterie_Parallelator/firmware/src/WebRouteSecurity.h

#ifndef WEB_ROUTE_SECURITY_H
#define WEB_ROUTE_SECURITY_H

bool isMutationRouteEnabled(const char *configuredToken);
bool isMutationTokenAuthorized(const char *providedToken,
                               const char *configuredToken);
bool isMutationAuthorizationHeaderAuthorized(const char *authorizationHeader,
                                             const char *configuredToken);

#endif // WEB_ROUTE_SECURITY_H
