KomplexKapharnaum/KXKM_Batterie_Parallelator/firmware/src/WiFiHandler.cpp

/*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
 * You should have received a copy of the GNU General Public License
 * along with this program. If not, see <https://www.gnu.org/licenses/>.
 */

/**
 * @file WiFiHandler.cpp
 * @brief Implémentation de la classe WiFiHandler pour gérer la connexion WiFi.
 * @details Créé par Clément Saillant pour Komplex Kapharnum assisté par IA.
 */

#include "WiFiHandler.h"
#include <KxLogger.h>

// Assurez-vous que `debugLogger` est déclaré et initialisé correctement
extern KxLogger debugLogger;

/**
 * @brief Constructeur de la classe WiFiHandler.
 * @param ssid Le SSID du réseau WiFi.
 * @param password Le mot de passe du réseau WiFi.
 */
WiFiHandler::WiFiHandler(const char *ssid, const char *password)
    : ssid(ssid), password(password) {}

/**
 * @brief Constructeur de la classe WiFiHandler pour les réseaux sans mot de passe.
 * @param ssid Le SSID du réseau WiFi.
 */
WiFiHandler::WiFiHandler(const char *ssid)
    : ssid(ssid), password(NULL) {}

/**
 * @brief Démarrer la connexion WiFi.
 */
void WiFiHandler::begin() {
  WiFi.mode(WIFI_STA);
  WiFi.setHostname("BatteryMonitor");

  if (password) {
    WiFi.begin(ssid, password);
  } else {
    WiFi.begin(ssid);
  }
  constexpr int kWifiTimeoutMs = 30000;
  int elapsed = 0;
  while (WiFi.status() != WL_CONNECTED && elapsed < kWifiTimeoutMs) {
    vTaskDelay(1000 / portTICK_PERIOD_MS);
    elapsed += 1000;
    debugLogger.println(KxLogger::WIFI,"Connecting to WiFi...");
  }
  if (WiFi.status() != WL_CONNECTED) {
    debugLogger.println(KxLogger::WIFI,"WiFi connection timeout after 30s");
    return;
  }
  debugLogger.println(KxLogger::WIFI,"=======================> Connected to WiFi");
  debugLogger.println(KxLogger::WIFI,WiFi.localIP().toString());
}

WiFiHandler::WiFiHandler() {}

void WiFiHandler::begin(const char* ssid, const char* password) {
    WiFi.begin(ssid, password);
    constexpr int kWifiTimeoutMs = 30000;
    int elapsed = 0;
    while (WiFi.status() != WL_CONNECTED && elapsed < kWifiTimeoutMs) {
        delay(1000);
        elapsed += 1000;
        Serial.println("Connecting to WiFi...");
    }
    if (WiFi.status() != WL_CONNECTED) {
        Serial.println("WiFi connection timeout");
        return;
    }
    Serial.println("Connected to WiFi");
}

bool WiFiHandler::isConnected() {
    return WiFi.status() == WL_CONNECTED;
}
