KomplexKapharnaum/KXKM_Batterie_Parallelator/firmware/src/pin_mapppings.h

#ifndef PIN_MAPPPINGS_H
#define PIN_MAPPPINGS_H

const int SDA_pin = 32;
const int SCL_pin = 33;

const uint8_t INA_ALERT_PIN[8] = {2, 3, 4, 5, 6, 7, 8, 9}; ///< Pin-Change used for INA "ALERT" functionality
                                                           // on<<<<

#endif // PIN_MAPPPINGS_H
