KomplexKapharnaum/KXKM_Batterie_Parallelator/firmware-idf/components/bmu_display/bmu_ui_config.cpp

#include "bmu_ui.h"
#include "bmu_config.h"
#include "bmu_wifi.h"
#include "bmu_ble.h"
#include "bsp/esp-bsp.h"
#include "esp_log.h"
#include <cstdio>
#include <cstring>

static const char *TAG = "UI_CFG";

static lv_obj_t *s_name_ta = NULL;
static lv_obj_t *s_ssid_ta = NULL;
static lv_obj_t *s_pass_ta = NULL;
static lv_obj_t *s_mqtt_ta = NULL;

/* Valeurs seuils — modifiées par les steppers */
static uint16_t s_v_min  = 24000;
static uint16_t s_v_max  = 30000;
static uint16_t s_i_max  = 10000;
static uint16_t s_v_diff = 1000;

static lv_obj_t *s_vmin_lbl  = NULL;
static lv_obj_t *s_vmax_lbl  = NULL;
static lv_obj_t *s_imax_lbl  = NULL;
static lv_obj_t *s_vdiff_lbl = NULL;

static lv_obj_t *s_ble_sw       = NULL;
static lv_obj_t *s_bright_slider = NULL;

static lv_obj_t *s_vrm_id_ta = NULL;
static lv_obj_t *s_vrm_sw = NULL;
static lv_obj_t *s_vic_key_ta = NULL;
static lv_obj_t *s_vic_sw = NULL;

/* Battery labels editing */
static int s_label_edit_idx = 0;
static lv_obj_t *s_label_idx_lbl = NULL;
static lv_obj_t *s_label_ta = NULL;

/* ------------------------------------------------------------------ */
/* Stepper                                                             */
/* ------------------------------------------------------------------ */

typedef struct {
    uint16_t   *value;
    uint16_t    min_val;
    uint16_t    max_val;
    uint16_t    step;
    lv_obj_t  **label;
    const char *fmt; /* used when display_as_volts == false */
    bool        display_as_volts;
} stepper_ctx_t;

static stepper_ctx_t s_steppers[4]; /* v_min, v_max, i_max, v_diff */

static void stepper_update_label(stepper_ctx_t *sc)
{
    char buf[24];
    if (sc->display_as_volts) {
        snprintf(buf, sizeof(buf), "%.2fV", *sc->value / 1000.0f);
    } else {
        snprintf(buf, sizeof(buf), sc->fmt, *sc->value);
    }
    lv_label_set_text(*sc->label, buf);
}

static void stepper_minus_cb(lv_event_t *e)
{
    stepper_ctx_t *sc = (stepper_ctx_t *)lv_event_get_user_data(e);
    if (*sc->value > sc->min_val) *sc->value -= sc->step;
    stepper_update_label(sc);
}

static void stepper_plus_cb(lv_event_t *e)
{
    stepper_ctx_t *sc = (stepper_ctx_t *)lv_event_get_user_data(e);
    if (*sc->value < sc->max_val) *sc->value += sc->step;
    stepper_update_label(sc);
}

static void create_stepper(lv_obj_t *parent, const char *label_text,
                            stepper_ctx_t *sc)
{
    lv_obj_t *row = lv_obj_create(parent);
    lv_obj_set_size(row, lv_pct(100), 28);
    lv_obj_set_flex_flow(row, LV_FLEX_FLOW_ROW);
    lv_obj_set_flex_align(row, LV_FLEX_ALIGN_START, LV_FLEX_ALIGN_CENTER, LV_FLEX_ALIGN_CENTER);
    lv_obj_set_style_bg_opa(row, LV_OPA_TRANSP, 0);
    lv_obj_set_style_border_width(row, 0, 0);
    lv_obj_set_style_pad_all(row, 0, 0);
    lv_obj_set_style_pad_column(row, 4, 0);

    /* Libellé gauche */
    lv_obj_t *lbl = lv_label_create(row);
    lv_label_set_text(lbl, label_text);
    lv_obj_set_style_text_color(lbl, UI_COLOR_TEXT_SEC, 0);
    lv_obj_set_width(lbl, 55);

    /* Bouton moins */
    lv_obj_t *btn_minus = lv_button_create(row);
    lv_obj_set_size(btn_minus, 28, 22);
    lv_obj_set_style_bg_color(btn_minus, UI_COLOR_CARD_ALT, 0);
    lv_obj_t *ml = lv_label_create(btn_minus);
    lv_label_set_text(ml, LV_SYMBOL_MINUS);
    lv_obj_center(ml);
    lv_obj_add_event_cb(btn_minus, stepper_minus_cb, LV_EVENT_CLICKED, sc);

    /* Libellé valeur */
    *sc->label = lv_label_create(row);
    lv_obj_set_style_text_color(*sc->label, UI_COLOR_TEXT, 0);
    lv_obj_set_width(*sc->label, 80);
    lv_obj_set_style_text_align(*sc->label, LV_TEXT_ALIGN_CENTER, 0);
    stepper_update_label(sc);

    /* Bouton plus */
    lv_obj_t *btn_plus = lv_button_create(row);
    lv_obj_set_size(btn_plus, 28, 22);
    lv_obj_set_style_bg_color(btn_plus, UI_COLOR_CARD_ALT, 0);
    lv_obj_t *pl = lv_label_create(btn_plus);
    lv_label_set_text(pl, LV_SYMBOL_PLUS);
    lv_obj_center(pl);
    lv_obj_add_event_cb(btn_plus, stepper_plus_cb, LV_EVENT_CLICKED, sc);
}

/* ------------------------------------------------------------------ */
/* Helpers section / textarea                                          */
/* ------------------------------------------------------------------ */

static lv_obj_t *section_label(lv_obj_t *parent, const char *text)
{
    lv_obj_t *lbl = lv_label_create(parent);
    lv_label_set_text(lbl, text);
    lv_obj_set_style_text_color(lbl, UI_COLOR_TEXT_DIM, 0);
    lv_obj_set_style_text_opa(lbl, LV_OPA_70, 0);
    lv_obj_set_width(lbl, lv_pct(100));
    return lbl;
}

static lv_obj_t *create_textarea(lv_obj_t *parent, const char *initial_text,
                                  bool password, int max_len)
{
    lv_obj_t *ta = lv_textarea_create(parent);
    lv_textarea_set_one_line(ta, true);
    lv_textarea_set_max_length(ta, max_len);
    lv_textarea_set_text(ta, initial_text ? initial_text : "");
    if (password) lv_textarea_set_password_mode(ta, true);
    lv_obj_set_width(ta, lv_pct(100));
    lv_obj_set_height(ta, 30);
    lv_obj_set_style_bg_color(ta, UI_COLOR_CARD, 0);
    lv_obj_set_style_text_color(ta, UI_COLOR_TEXT, 0);
    lv_obj_set_style_border_color(ta, UI_COLOR_BORDER, 0);
    return ta;
}

/* ------------------------------------------------------------------ */
/* API publique                                                        */
/* ------------------------------------------------------------------ */

void bmu_ui_config_create(lv_obj_t *parent)
{
    lv_obj_set_style_bg_color(parent, UI_COLOR_BG, 0);

    /* Conteneur scrollable */
    lv_obj_t *cont = lv_obj_create(parent);
    lv_obj_set_size(cont, 312, 210);
    lv_obj_align(cont, LV_ALIGN_TOP_MID, 0, 0);
    lv_obj_set_flex_flow(cont, LV_FLEX_FLOW_COLUMN);
    lv_obj_set_style_pad_row(cont, 4, 0);
    lv_obj_set_style_pad_all(cont, 4, 0);
    lv_obj_set_style_bg_color(cont, UI_COLOR_BG, 0);
    lv_obj_set_style_border_width(cont, 0, 0);
    lv_obj_add_flag(cont, LV_OBJ_FLAG_SCROLLABLE);

    /* --- Section : Nom appareil --- */
    section_label(cont, "NOM APPAREIL");
    s_name_ta = create_textarea(cont, bmu_config_get_device_name(), false, 31);

    /* --- Section : WiFi --- */
    section_label(cont, "WIFI");
    s_ssid_ta = create_textarea(cont, bmu_config_get_wifi_ssid(), false, 31);
    s_pass_ta = create_textarea(cont, bmu_config_get_wifi_password(), true, 63);

    /* --- Section : Seuils protection --- */
    section_label(cont, "SEUILS PROTECTION");
    bmu_config_get_thresholds(&s_v_min, &s_v_max, &s_i_max, &s_v_diff);

    s_steppers[0] = {&s_v_min,  20000, 30000,  500, &s_vmin_lbl,  "%u mV", true};
    s_steppers[1] = {&s_v_max,  25000, 35000,  500, &s_vmax_lbl,  "%u mV", true};
    s_steppers[2] = {&s_i_max,   1000, 50000, 1000, &s_imax_lbl,  "%u mA", false};
    s_steppers[3] = {&s_v_diff,   100,  5000,  100, &s_vdiff_lbl, "%u mV", true};

    create_stepper(cont, "V min",  &s_steppers[0]);
    create_stepper(cont, "V max",  &s_steppers[1]);
    create_stepper(cont, "I max",  &s_steppers[2]);
    create_stepper(cont, "V diff", &s_steppers[3]);

    /* --- Section : MQTT --- */
    section_label(cont, "MQTT");
    s_mqtt_ta = create_textarea(cont, bmu_config_get_mqtt_uri(), false, 63);

    /* --- Section : Options --- */
    section_label(cont, "OPTIONS");

    /* Ligne BLE */
    lv_obj_t *ble_row = lv_obj_create(cont);
    lv_obj_set_size(ble_row, lv_pct(100), 28);
    lv_obj_set_flex_flow(ble_row, LV_FLEX_FLOW_ROW);
    lv_obj_set_flex_align(ble_row, LV_FLEX_ALIGN_SPACE_BETWEEN, LV_FLEX_ALIGN_CENTER, LV_FLEX_ALIGN_CENTER);
    lv_obj_set_style_bg_opa(ble_row, LV_OPA_TRANSP, 0);
    lv_obj_set_style_border_width(ble_row, 0, 0);
    lv_obj_set_style_pad_all(ble_row, 0, 0);
    lv_obj_t *ble_lbl = lv_label_create(ble_row);
    lv_label_set_text(ble_lbl, "BLE BMU");
    lv_obj_set_style_text_color(ble_lbl, UI_COLOR_TEXT_SEC, 0);
    s_ble_sw = lv_switch_create(ble_row);
    lv_obj_set_style_bg_color(s_ble_sw, UI_COLOR_OK, (lv_style_selector_t)LV_PART_INDICATOR | (lv_style_selector_t)LV_STATE_CHECKED);
#if CONFIG_BMU_BLE_ENABLED
    lv_obj_add_state(s_ble_sw, LV_STATE_CHECKED);
#endif
    lv_obj_add_state(s_ble_sw, LV_STATE_DISABLED);

    /* Bouton : ouvrir une fenêtre de réappairage BLE (audit sécu).
     * Hors fenêtre, un appareil appairé ne peut pas écraser son bond.
     * L'opérateur tape ici juste avant de réappairer depuis le téléphone. */
    lv_obj_t *repair_btn = lv_btn_create(cont);
    lv_obj_set_width(repair_btn, lv_pct(100));
    lv_obj_set_style_bg_color(repair_btn, UI_COLOR_SOLAR, 0);
    lv_obj_t *rb_lbl = lv_label_create(repair_btn);
    lv_label_set_text(rb_lbl, LV_SYMBOL_BLUETOOTH " Autoriser reappairage 30s");
    lv_obj_center(rb_lbl);
    lv_obj_add_event_cb(repair_btn, [](lv_event_t *e) {
        lv_obj_t *btn = (lv_obj_t *)lv_event_get_target(e);
        bmu_ble_allow_repair(30000);
        lv_obj_t *lbl = lv_obj_get_child(btn, 0);
        if (lbl) lv_label_set_text(lbl, LV_SYMBOL_OK " Fenetre ouverte 30s");
    }, LV_EVENT_CLICKED, NULL);

    /* Ligne luminosité */
    lv_obj_t *br_row = lv_obj_create(cont);
    lv_obj_set_size(br_row, lv_pct(100), 28);
    lv_obj_set_flex_flow(br_row, LV_FLEX_FLOW_ROW);
    lv_obj_set_flex_align(br_row, LV_FLEX_ALIGN_START, LV_FLEX_ALIGN_CENTER, LV_FLEX_ALIGN_CENTER);
    lv_obj_set_style_bg_opa(br_row, LV_OPA_TRANSP, 0);
    lv_obj_set_style_border_width(br_row, 0, 0);
    lv_obj_set_style_pad_all(br_row, 0, 0);
    lv_obj_set_style_pad_column(br_row, 8, 0);
    lv_obj_t *br_lbl = lv_label_create(br_row);
    lv_label_set_text(br_lbl, LV_SYMBOL_IMAGE " Lum");
    lv_obj_set_style_text_color(br_lbl, UI_COLOR_TEXT_SEC, 0);
    s_bright_slider = lv_slider_create(br_row);
    lv_slider_set_range(s_bright_slider, 10, 100);
    lv_slider_set_value(s_bright_slider, 100, LV_ANIM_OFF);
    lv_obj_set_width(s_bright_slider, 180);
    lv_obj_set_style_bg_color(s_bright_slider, UI_COLOR_SOLAR, LV_PART_INDICATOR);
    lv_obj_add_event_cb(s_bright_slider, [](lv_event_t *e) {
        lv_obj_t *slider = (lv_obj_t *)lv_event_get_target(e);
        int val = lv_slider_get_value(slider);
        bsp_display_brightness_set(val);
    }, LV_EVENT_VALUE_CHANGED, NULL);

    /* --- Section : Noms batteries --- */
    section_label(cont, "NOMS BATTERIES");

    /* Ligne sélecteur d'index : [<] B1 [>] + textarea */
    lv_obj_t *label_row = lv_obj_create(cont);
    lv_obj_set_size(label_row, lv_pct(100), 30);
    lv_obj_set_flex_flow(label_row, LV_FLEX_FLOW_ROW);
    lv_obj_set_flex_align(label_row, LV_FLEX_ALIGN_START, LV_FLEX_ALIGN_CENTER, LV_FLEX_ALIGN_CENTER);
    lv_obj_set_style_bg_opa(label_row, LV_OPA_TRANSP, 0);
    lv_obj_set_style_border_width(label_row, 0, 0);
    lv_obj_set_style_pad_all(label_row, 0, 0);
    lv_obj_set_style_pad_column(label_row, 4, 0);

    /* Bouton précédent */
    lv_obj_t *btn_prev = lv_button_create(label_row);
    lv_obj_set_size(btn_prev, 28, 24);
    lv_obj_set_style_bg_color(btn_prev, UI_COLOR_CARD_ALT, 0);
    lv_obj_t *prev_lbl = lv_label_create(btn_prev);
    lv_label_set_text(prev_lbl, LV_SYMBOL_LEFT);
    lv_obj_center(prev_lbl);

    /* Libellé index "B1" */
    s_label_idx_lbl = lv_label_create(label_row);
    lv_label_set_text(s_label_idx_lbl, "B1");
    lv_obj_set_style_text_color(s_label_idx_lbl, UI_COLOR_INFO, 0);
    lv_obj_set_width(s_label_idx_lbl, 32);
    lv_obj_set_style_text_align(s_label_idx_lbl, LV_TEXT_ALIGN_CENTER, 0);

    /* Bouton suivant */
    lv_obj_t *btn_next = lv_button_create(label_row);
    lv_obj_set_size(btn_next, 28, 24);
    lv_obj_set_style_bg_color(btn_next, UI_COLOR_CARD_ALT, 0);
    lv_obj_t *next_lbl = lv_label_create(btn_next);
    lv_label_set_text(next_lbl, LV_SYMBOL_RIGHT);
    lv_obj_center(next_lbl);

    /* Textarea du nom de batterie */
    s_label_ta = lv_textarea_create(label_row);
    lv_textarea_set_one_line(s_label_ta, true);
    lv_textarea_set_max_length(s_label_ta, 8);
    lv_textarea_set_text(s_label_ta, bmu_config_get_battery_label(0));
    lv_obj_set_width(s_label_ta, 120);
    lv_obj_set_height(s_label_ta, 26);
    lv_obj_set_style_bg_color(s_label_ta, UI_COLOR_CARD, 0);
    lv_obj_set_style_text_color(s_label_ta, UI_COLOR_TEXT, 0);
    lv_obj_set_style_border_color(s_label_ta, UI_COLOR_BORDER, 0);

    lv_obj_add_event_cb(btn_prev, [](lv_event_t *e) {
        (void)e;
        const char *txt = lv_textarea_get_text(s_label_ta);
        if (txt && txt[0] != '\0') bmu_config_set_battery_label(s_label_edit_idx, txt);
        if (s_label_edit_idx > 0) s_label_edit_idx--;
        char idx_buf[16];
        snprintf(idx_buf, sizeof(idx_buf), "B%d", s_label_edit_idx + 1);
        lv_label_set_text(s_label_idx_lbl, idx_buf);
        lv_textarea_set_text(s_label_ta, bmu_config_get_battery_label(s_label_edit_idx));
    }, LV_EVENT_CLICKED, NULL);

    lv_obj_add_event_cb(btn_next, [](lv_event_t *e) {
        (void)e;
        const char *txt = lv_textarea_get_text(s_label_ta);
        if (txt && txt[0] != '\0') bmu_config_set_battery_label(s_label_edit_idx, txt);
        if (s_label_edit_idx < (BMU_MAX_BATTERIES - 1)) s_label_edit_idx++;
        char idx_buf[16];
        snprintf(idx_buf, sizeof(idx_buf), "B%d", s_label_edit_idx + 1);
        lv_label_set_text(s_label_idx_lbl, idx_buf);
        lv_textarea_set_text(s_label_ta, bmu_config_get_battery_label(s_label_edit_idx));
    }, LV_EVENT_CLICKED, NULL);

    /* --- Section : Victron --- */
    section_label(cont, "VICTRON");

    s_vrm_id_ta = create_textarea(cont, bmu_config_get_vrm_portal_id(), false, 19);

    lv_obj_t *vrm_row = lv_obj_create(cont);
    lv_obj_set_size(vrm_row, lv_pct(100), 28);
    lv_obj_set_flex_flow(vrm_row, LV_FLEX_FLOW_ROW);
    lv_obj_set_flex_align(vrm_row, LV_FLEX_ALIGN_SPACE_BETWEEN, LV_FLEX_ALIGN_CENTER, LV_FLEX_ALIGN_CENTER);
    lv_obj_set_style_bg_opa(vrm_row, LV_OPA_TRANSP, 0);
    lv_obj_set_style_border_width(vrm_row, 0, 0);
    lv_obj_set_style_pad_all(vrm_row, 0, 0);
    lv_obj_t *vrm_lbl = lv_label_create(vrm_row);
    lv_label_set_text(vrm_lbl, "VRM Cloud");
    lv_obj_set_style_text_color(vrm_lbl, UI_COLOR_TEXT_SEC, 0);
    s_vrm_sw = lv_switch_create(vrm_row);
    if (bmu_config_get_vrm_enabled()) lv_obj_add_state(s_vrm_sw, LV_STATE_CHECKED);

    s_vic_key_ta = create_textarea(cont, bmu_config_get_victron_ble_key(), false, 32);

    lv_obj_t *vic_row = lv_obj_create(cont);
    lv_obj_set_size(vic_row, lv_pct(100), 28);
    lv_obj_set_flex_flow(vic_row, LV_FLEX_FLOW_ROW);
    lv_obj_set_flex_align(vic_row, LV_FLEX_ALIGN_SPACE_BETWEEN, LV_FLEX_ALIGN_CENTER, LV_FLEX_ALIGN_CENTER);
    lv_obj_set_style_bg_opa(vic_row, LV_OPA_TRANSP, 0);
    lv_obj_set_style_border_width(vic_row, 0, 0);
    lv_obj_set_style_pad_all(vic_row, 0, 0);
    lv_obj_t *vic_lbl = lv_label_create(vic_row);
    lv_label_set_text(vic_lbl, "BLE Victron");
    lv_obj_set_style_text_color(vic_lbl, UI_COLOR_TEXT_SEC, 0);
    s_vic_sw = lv_switch_create(vic_row);
    if (bmu_config_get_victron_ble_enabled()) lv_obj_add_state(s_vic_sw, LV_STATE_CHECKED);

    /* --- Bouton Sauvegarder --- */
    lv_obj_t *save_btn = lv_button_create(cont);
    lv_obj_set_size(save_btn, lv_pct(100), 36);
    lv_obj_set_style_bg_color(save_btn, lv_color_hex(0x00CC44), 0);
    lv_obj_t *save_lbl = lv_label_create(save_btn);
    lv_label_set_text(save_lbl, LV_SYMBOL_SAVE " SAUVEGARDER");
    lv_obj_set_style_text_color(save_lbl, lv_color_hex(0x000000), 0);
    lv_obj_center(save_lbl);
    lv_obj_add_event_cb(save_btn, [](lv_event_t *e) {
        (void)e;
        /* Sauvegarde du nom de batterie en cours d'édition */
        const char *lbl_txt = lv_textarea_get_text(s_label_ta);
        if (lbl_txt && lbl_txt[0] != '\0') bmu_config_set_battery_label(s_label_edit_idx, lbl_txt);
        bmu_config_save_battery_labels();
        bmu_config_set_device_name(lv_textarea_get_text(s_name_ta));
        bmu_config_set_wifi(lv_textarea_get_text(s_ssid_ta),
                            lv_textarea_get_text(s_pass_ta));
        bmu_config_set_thresholds(s_v_min, s_v_max, s_i_max, s_v_diff);
        bmu_config_set_mqtt_uri(lv_textarea_get_text(s_mqtt_ta));
        bmu_config_set_vrm_portal_id(lv_textarea_get_text(s_vrm_id_ta));
        bmu_config_set_vrm_enabled(lv_obj_has_state(s_vrm_sw, LV_STATE_CHECKED));
        bmu_config_set_victron_ble_key(lv_textarea_get_text(s_vic_key_ta));
        bmu_config_set_victron_ble_enabled(lv_obj_has_state(s_vic_sw, LV_STATE_CHECKED));
        ESP_LOGI("UI_CFG", "Config sauvegardee dans NVS");
    }, LV_EVENT_CLICKED, NULL);

    ESP_LOGI(TAG, "Config screen cree");
}

void bmu_ui_config_update(void)
{
    /* Ecran majoritairement statique — rien à rafraîchir */
}
